8076ducc/robocup-2024/open/mechanical design/camera/raspi spacer.stl

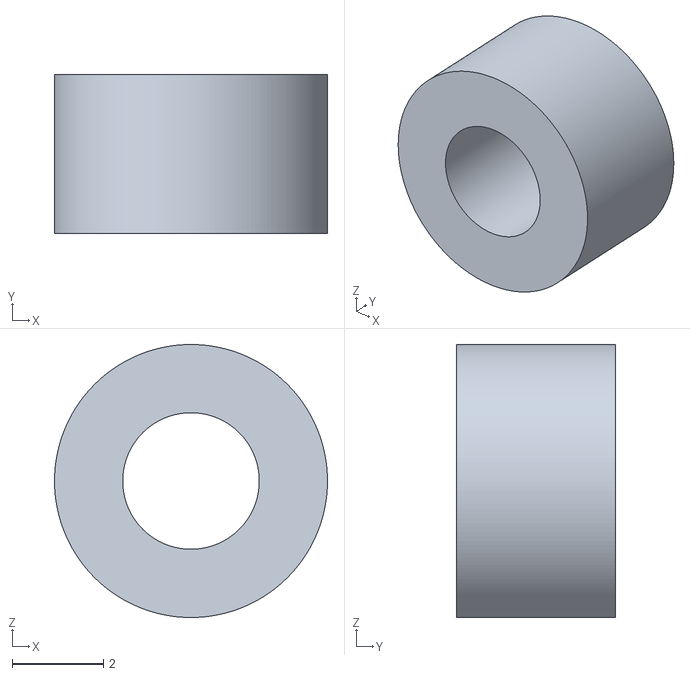
[picture p16: CAD file, 2024-03-23]
open/mechanical design/camera/raspi spacer.stl
6.00 x 3.50 x 6.00
