8076ducc/robocup-2024/open/mechanical design/cycloidal drive/gearbox cover.stl

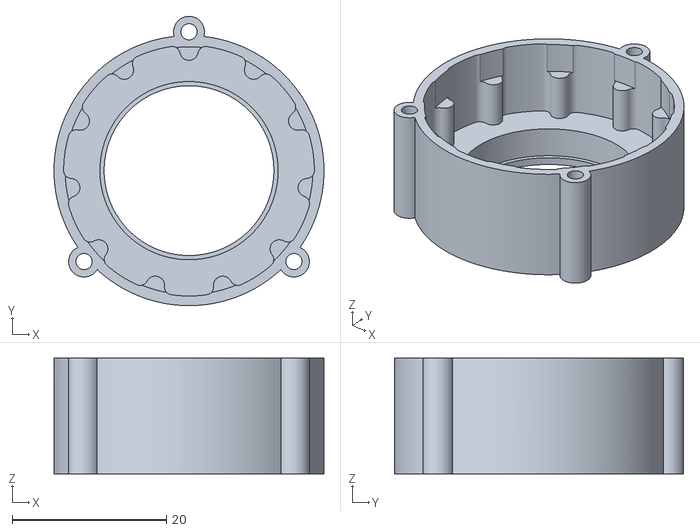
[picture p17: CAD file, 2023-11-01]
open/mechanical design/cycloidal drive/gearbox cover.stl
35.0 x 37.5 x 15.0
