8076ducc/robocup-2024/open/mechanical design/dribbler/dribbler mount.stl

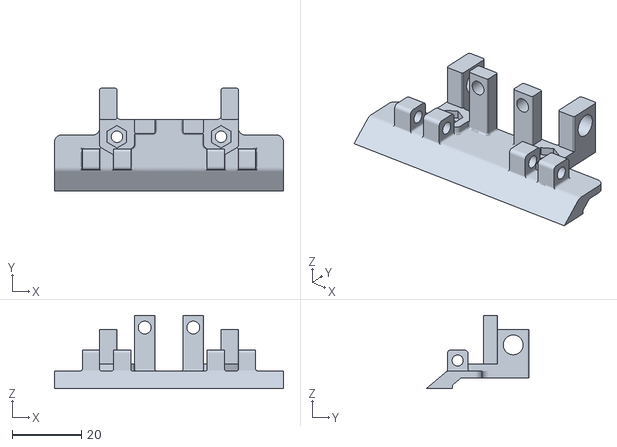
[picture p18: CAD file, 2024-04-01]
open/mechanical design/dribbler/dribbler mount.stl
66.0 x 29.6 x 21.1
