8076ducc/robocup-2024/open/mechanical design/dribbler/mould/big mould.stl

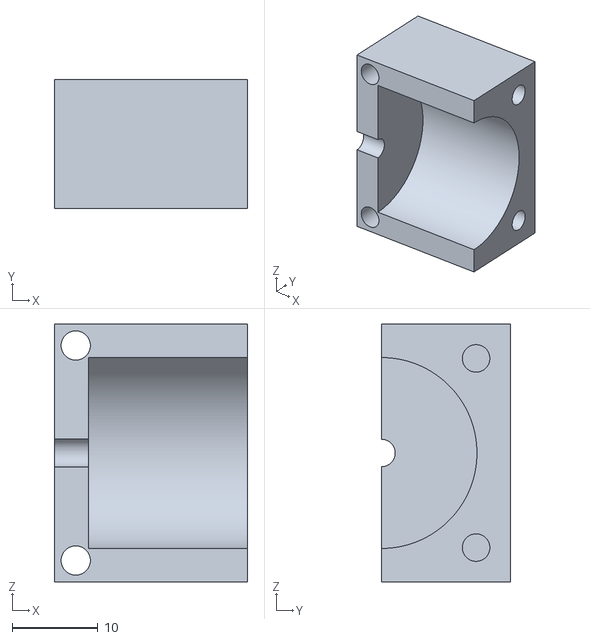
[picture p19: CAD file, 2024-04-05]
open/mechanical design/dribbler/mould/big mould.stl
22.5 x 15.0 x 30.0
