8076ducc/robocup-2024/open/mechanical design/dribbler/test/bearing hole test 6.2.stl

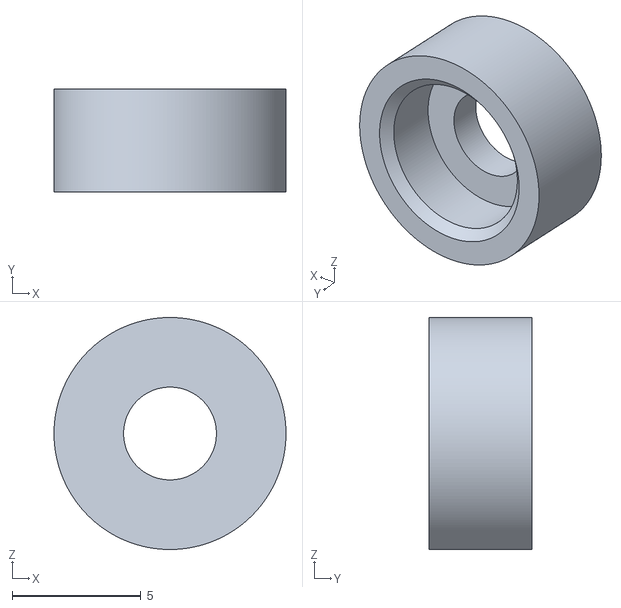
[picture p20: CAD file, 2024-04-04]
open/mechanical design/dribbler/test/bearing hole test 6.2.stl
9.00 x 4.00 x 9.00
