8076ducc/robocup-2024/open/mechanical design/dribbler/v2/gear shield.stl

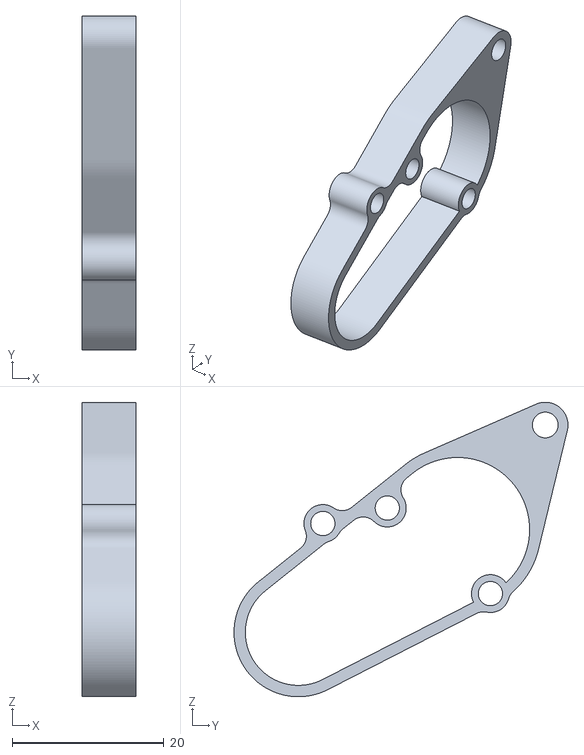
[picture p21: CAD file, 2024-05-06]
open/mechanical design/dribbler/v2/gear shield.stl
7.10 x 44.1 x 38.9
