8076ducc/robocup-2024/open/mechanical design/misc/camera aligner.stl

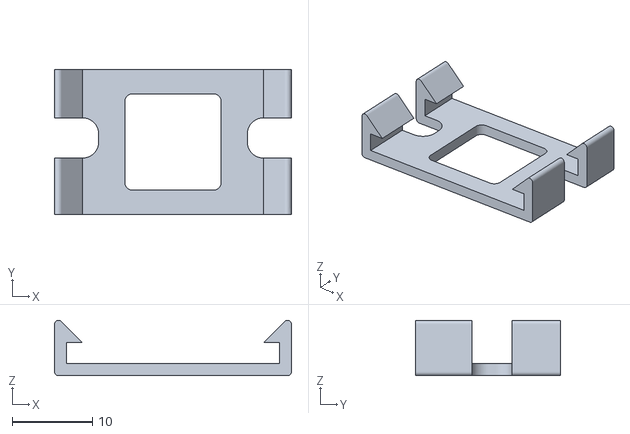
[picture p22: CAD file, 2024-04-01]
open/mechanical design/misc/camera aligner.stl
29.5 x 18.0 x 6.89
