8076ducc/robocup-2024/open/mechanical design/omniwheel/motor spacer.stl

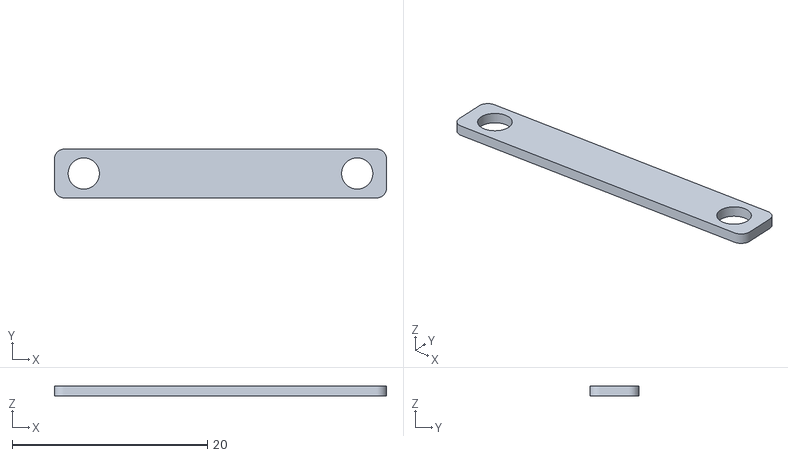
[picture p23: CAD file, 2024-04-01]
open/mechanical design/omniwheel/motor spacer.stl
34.0 x 5.00 x 1.00
