8076ducc/robocup-2024/open/mechanical design/plates/driver/fabrication drawing.dxf

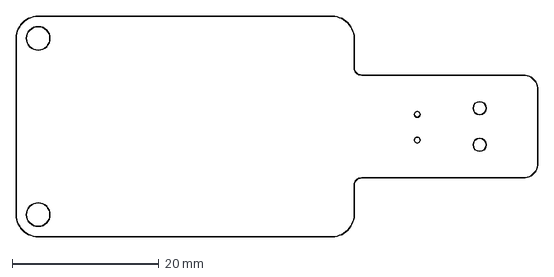
[picture p24: CAD file, 2023-12-15]
open/mechanical design/plates/driver/fabrication drawing.dxf
71.0 x 30.0 mm
