8076ducc/robocup-2024/open/mechanical design/plates/layer 2/fabrication drawing.dxf

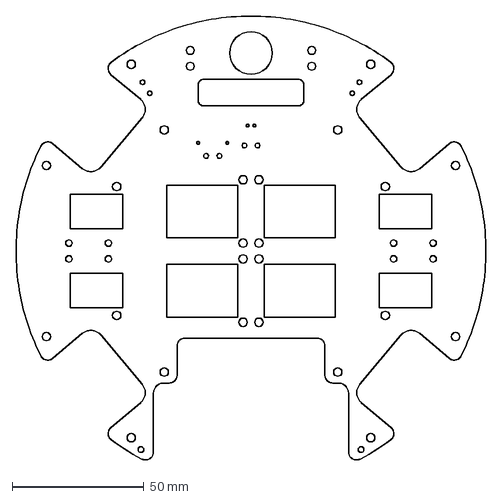
[picture p25: CAD file, 2023-12-15]
open/mechanical design/plates/layer 2/fabrication drawing.dxf
178.0 x 168.1 mm
