8076ducc/robocup-2024/open/mechanical design/plates/layer 3/outline.dxf

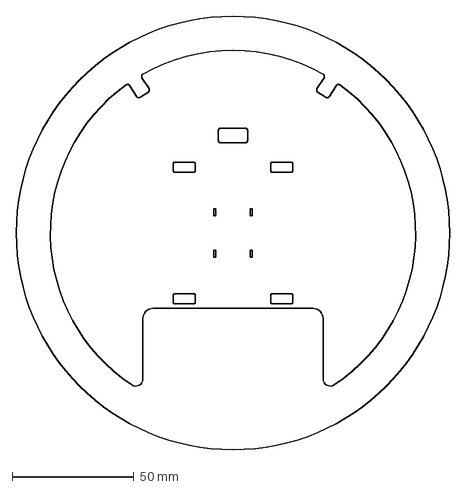
[picture p26: CAD file, 2023-12-17]
open/mechanical design/plates/layer 3/outline.dxf
178.0 x 178.0 mm
