8076ducc/robocup-2024/open/mechanical design/plates/layer 4/layer 4.dxf

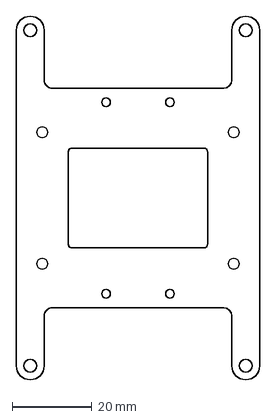
[picture p27: CAD file, 2024-03-23]
open/mechanical design/plates/layer 4/layer 4.dxf
61.0 x 91.2 mm
