8076ducc/robocup-2024/open/mechanical design/plates/Seeed XIAO/drawing.dxf

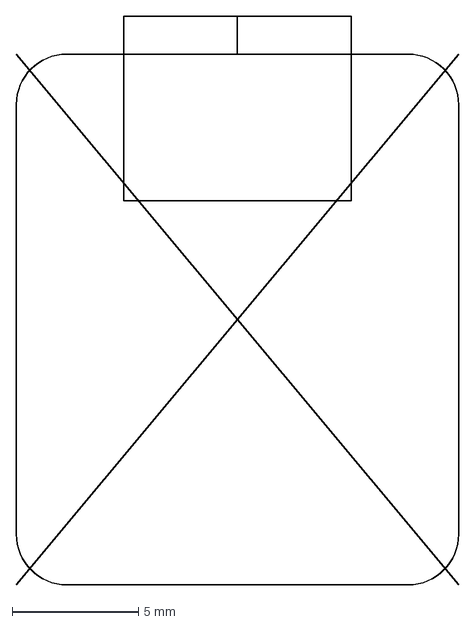
[picture p28: CAD file, 2023-11-23]
open/mechanical design/plates/Seeed XIAO/drawing.dxf
17.5 x 22.5 mm
