8076ducc/robocup-2024/open/mechanical design/shrouds/layer 2 shroud.stl

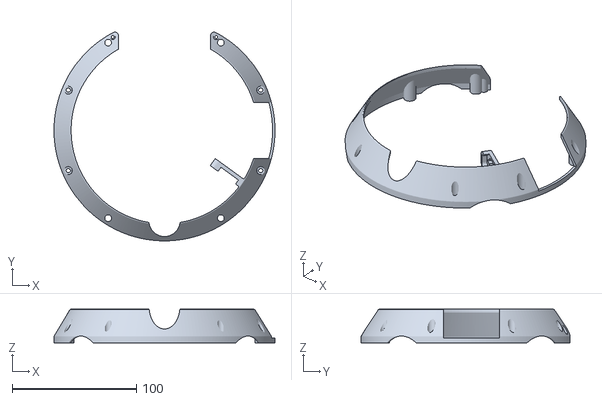
[picture p29: CAD file, 2024-08-02]
open/mechanical design/shrouds/layer 2 shroud.stl
178.0 x 168.1 x 27.0
