8076ducc/robocup-2024/mechanical design/dribbler/dribbler mount v29.stl

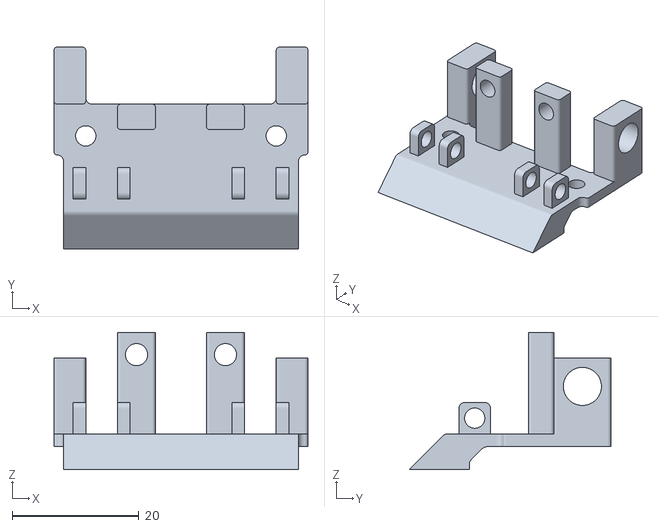
[picture p30: CAD file, 2024-01-17]
mechanical design/dribbler/dribbler mount v29.stl
40.0 x 31.8 x 21.6
