8076ducc/robocup-2024/open/mechanical design/ball puncher/puncher ramp.stl

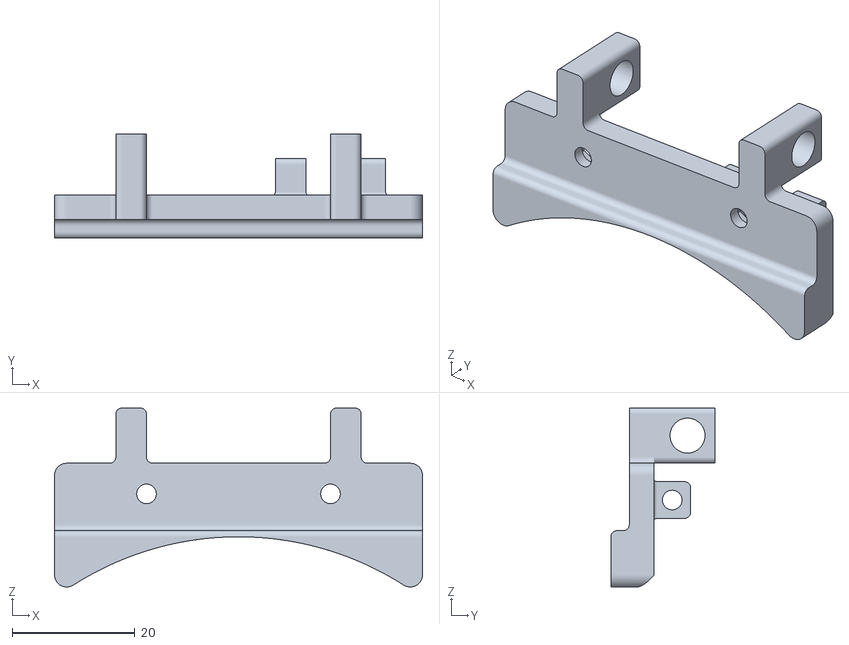
[picture p31: CAD file, 2024-05-06]
open/mechanical design/ball puncher/puncher ramp.stl
60.0 x 17.0 x 29.2
