8076ducc/robocup-2024/open/mechanical design/cycloidal drive/gearbox mount.stl

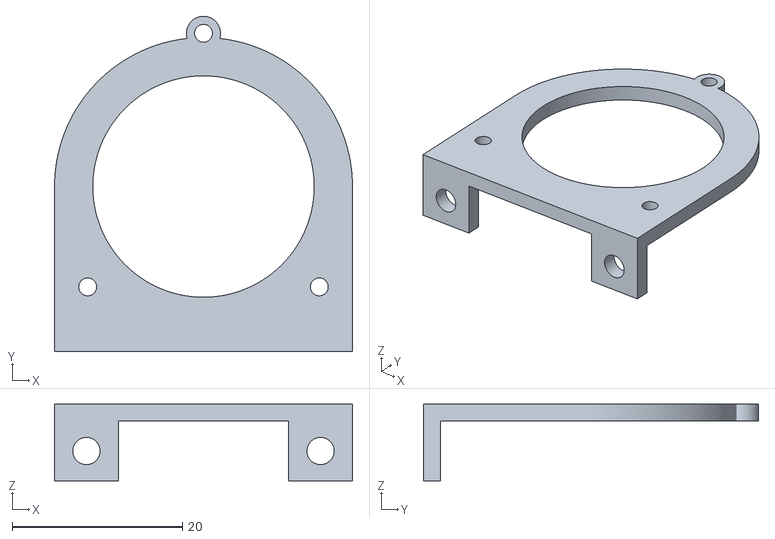
[picture p32: CAD file, 2023-11-01]
open/mechanical design/cycloidal drive/gearbox mount.stl
35.0 x 39.4 x 9.00
