8076ducc/robocup-2024/open/mechanical design/dribbler/gear shield.stl

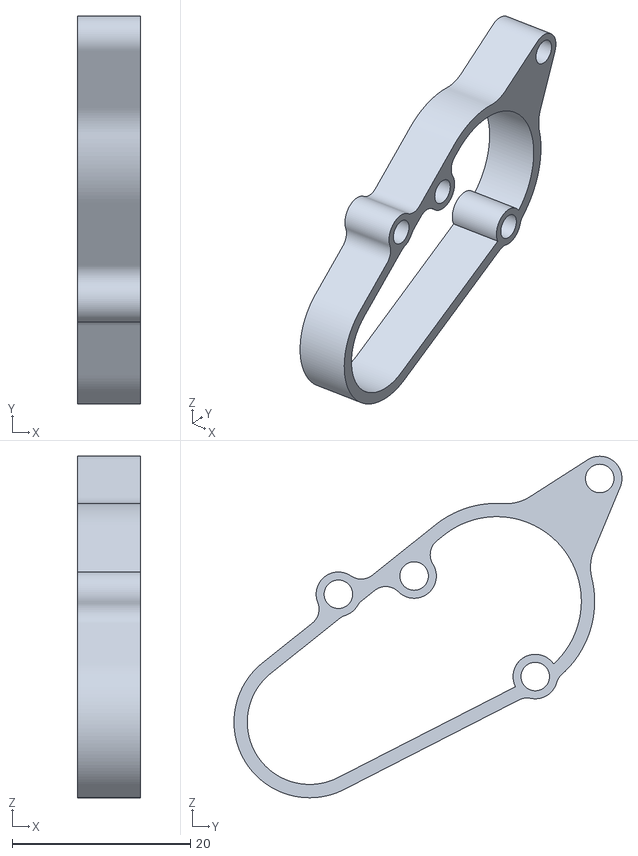
[picture p33: CAD file, 2024-04-01]
open/mechanical design/dribbler/gear shield.stl
7.10 x 43.6 x 38.4
