8076ducc/robocup-2024/open/mechanical design/dribbler/mould/small mould.stl

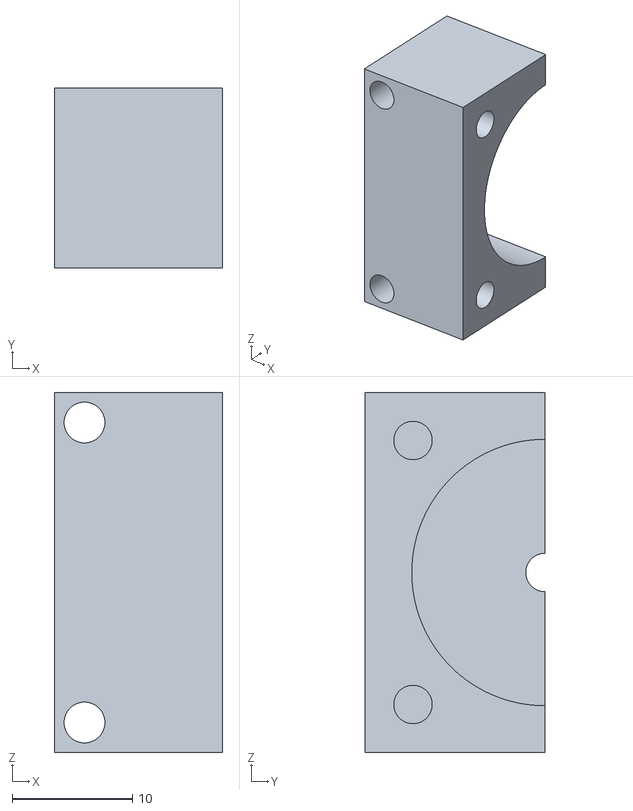
[picture p34: CAD file, 2024-02-21]
open/mechanical design/dribbler/mould/small mould.stl
14.0 x 15.0 x 30.0
