8076ducc/robocup-2024/open/mechanical design/dribbler/v2/plate (right).stl

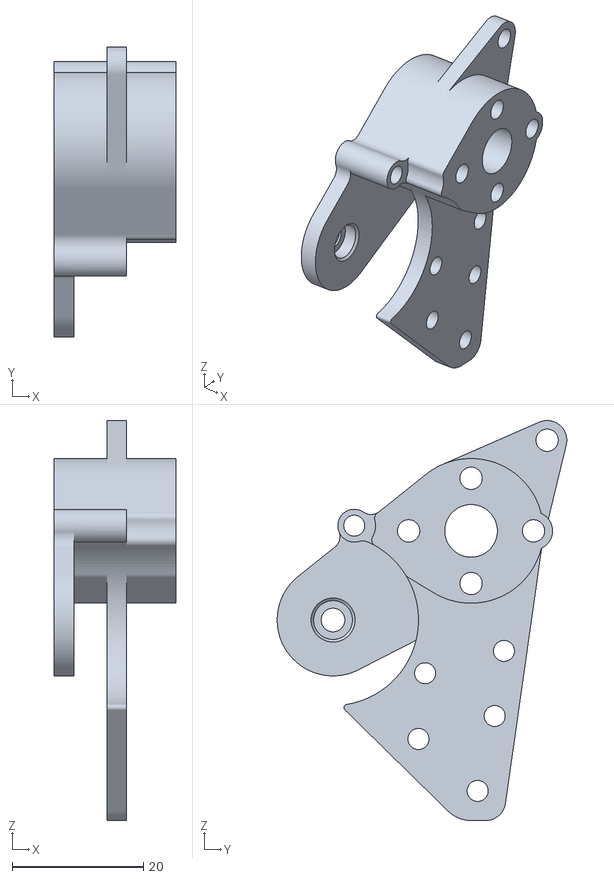
[picture p35: CAD file, 2024-04-05]
open/mechanical design/dribbler/v2/plate (right).stl
18.5 x 44.1 x 60.8
