8076ducc/robocup-2024/open/mechanical design/misc/wire clip.stl

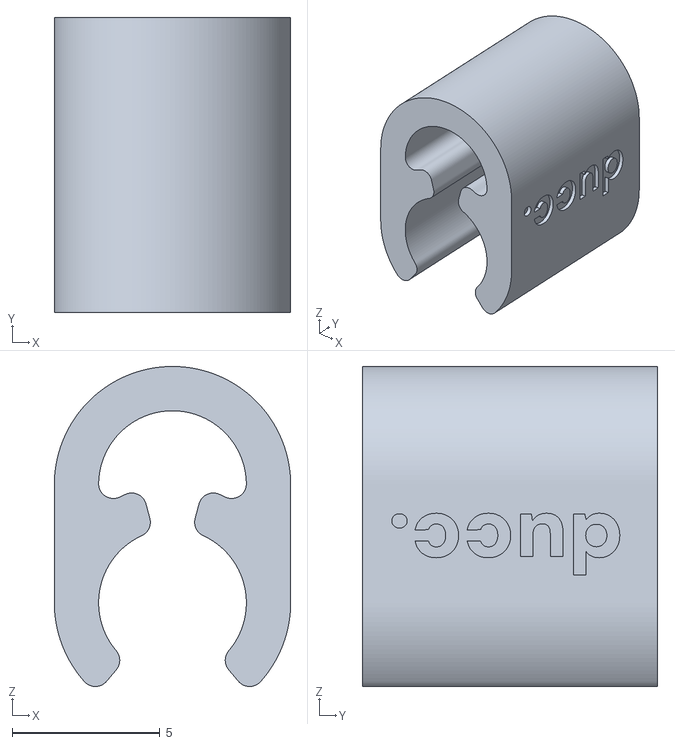
[picture p36: CAD file, 2024-03-23]
open/mechanical design/misc/wire clip.stl
8.00 x 10.0 x 10.8
