8076ducc/robocup-2024/open/mechanical design/omniwheel/roller.stl

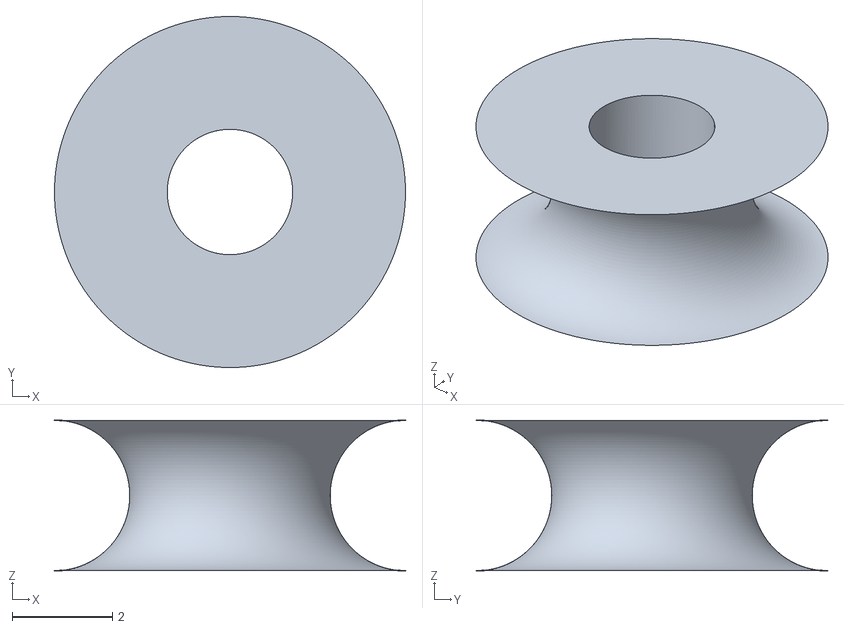
[picture p37: CAD file, 2024-04-01]
open/mechanical design/omniwheel/roller.stl
7.00 x 7.00 x 3.00
