8076ducc/robocup-2024/open/mechanical design/plates/layer 3/fabrication drawing.dxf

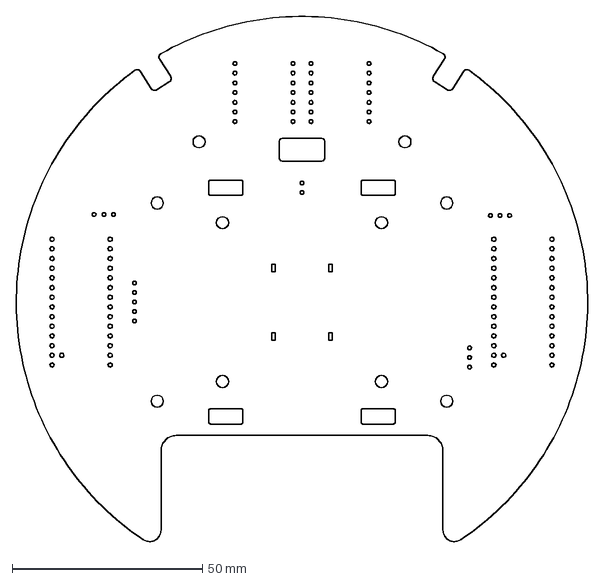
[picture p39: CAD file, 2023-12-15]
open/mechanical design/plates/layer 3/fabrication drawing.dxf
150.0 x 137.9 mm
