8076ducc/robocup-2024/open/mechanical design/plates/layer 4/layer 4.5.dxf

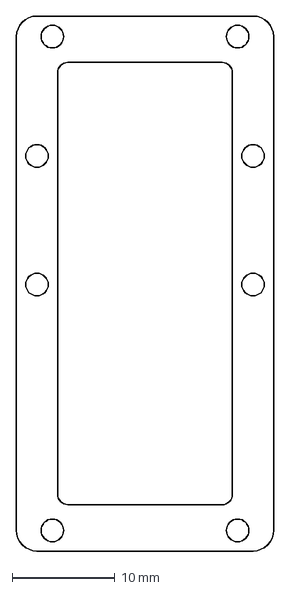
[picture p40: CAD file, 2024-03-23]
open/mechanical design/plates/layer 4/layer 4.5.dxf
25.0 x 52.0 mm
