8076ducc/robocup-2024/open/mechanical design/shrouds/layer 1 short cover.stl

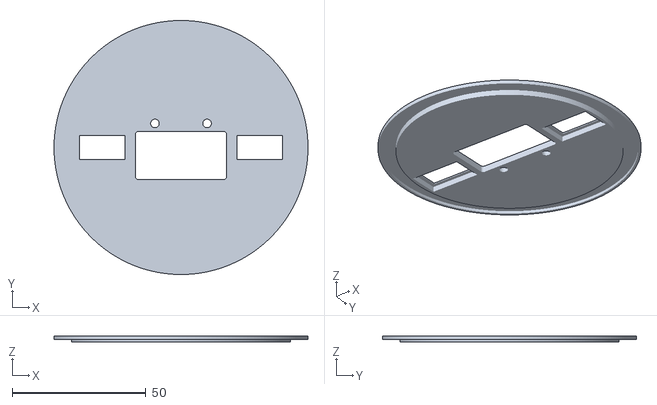
[picture p41: CAD file, 2024-08-02]
open/mechanical design/shrouds/layer 1 short cover.stl
95.0 x 95.0 x 2.40
