8076ducc/robocup-2024/mechanical design/dribbler/spacer.stl

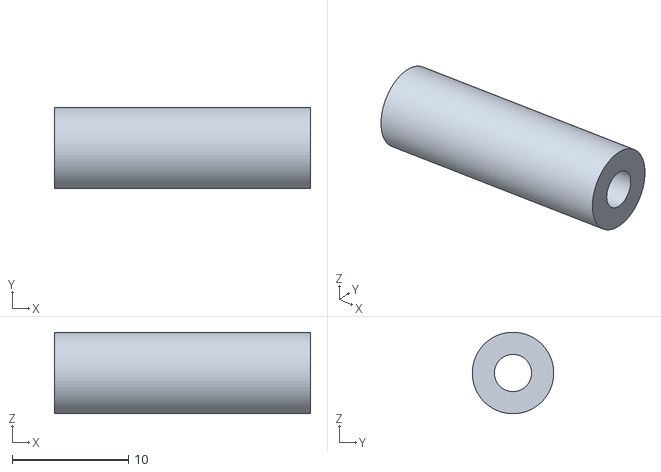
[picture p42: CAD file, 2024-01-17]
mechanical design/dribbler/spacer.stl
22.0 x 7.00 x 7.00
