8076ducc/robocup-2024/open/mechanical design/ball puncher/plate (right).stl

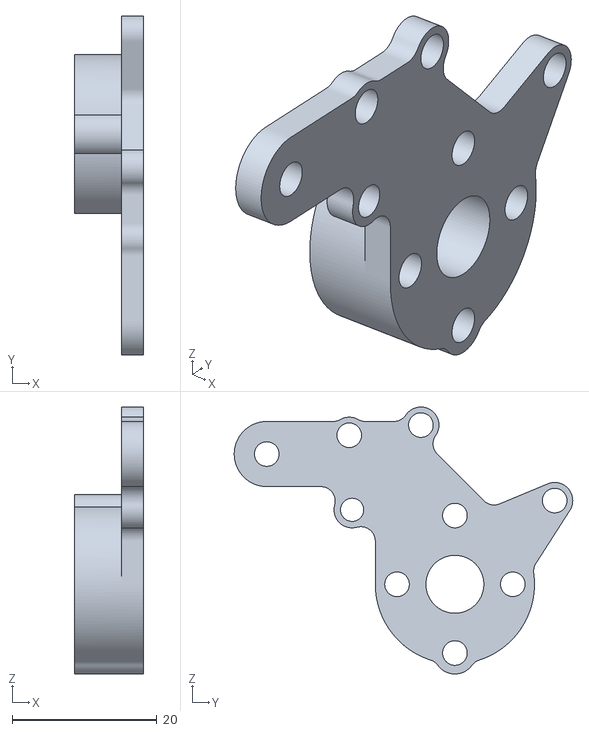
[picture p43: CAD file, 2024-05-06]
open/mechanical design/ball puncher/plate (right).stl
9.50 x 46.8 x 36.9
