8076ducc/robocup-2024/open/mechanical design/cycloidal drive/motor mount.stl

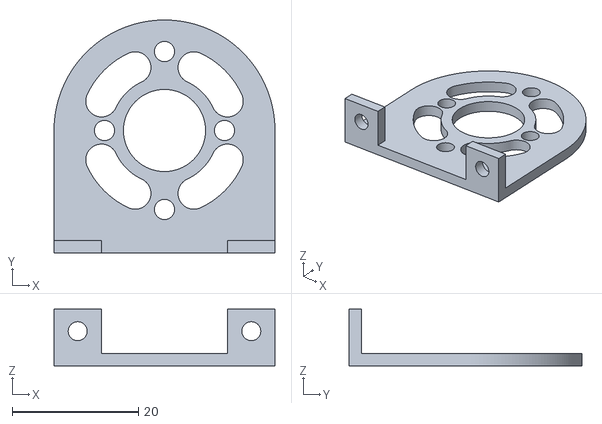
[picture p44: CAD file, 2023-11-01]
open/mechanical design/cycloidal drive/motor mount.stl
35.0 x 36.9 x 9.00
