8076ducc/robocup-2024/open/mechanical design/dribbler/emax spacer.stl

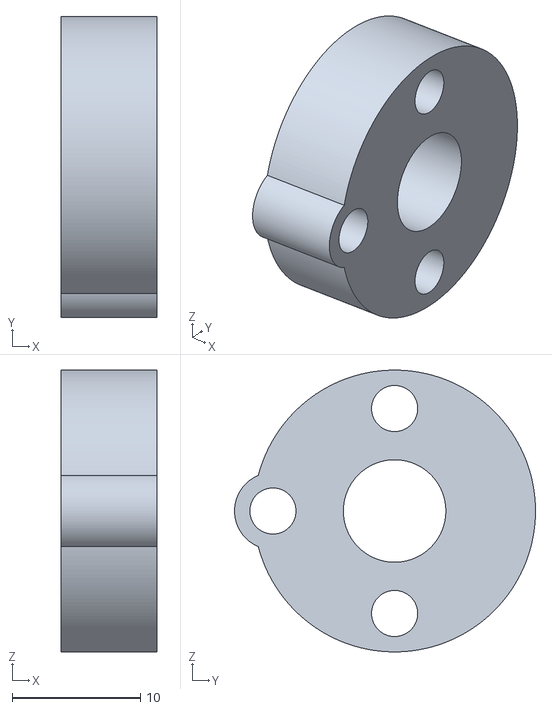
[picture p45: CAD file, 2024-04-01]
open/mechanical design/dribbler/emax spacer.stl
7.50 x 23.5 x 22.0
