8076ducc/robocup-2024/open/mechanical design/dribbler/mould/big roller.stl

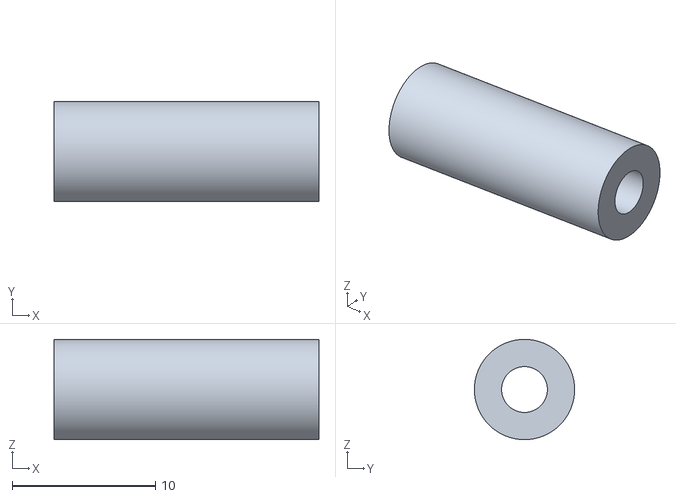
[picture p46: CAD file, 2024-02-21]
open/mechanical design/dribbler/mould/big roller.stl
18.5 x 7.00 x 7.00
