8076ducc/robocup-2024/open/mechanical design/dribbler/v2/clasp.stl

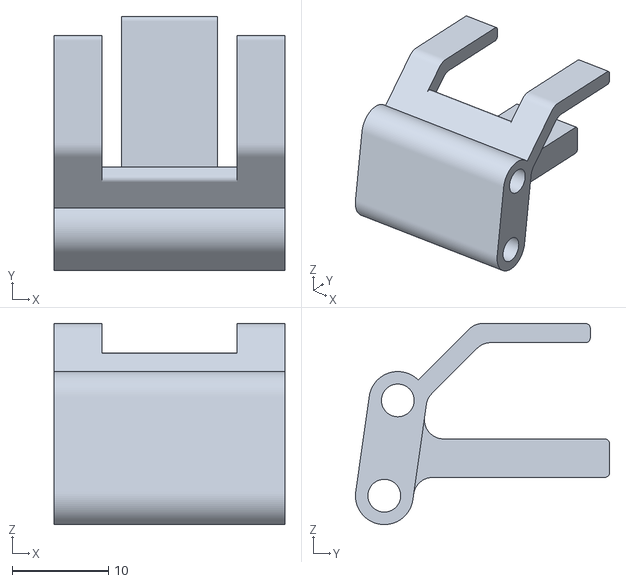
[picture p47: CAD file, 2024-04-05]
open/mechanical design/dribbler/v2/clasp.stl
24.0 x 26.4 x 20.9
