8076ducc/robocup-2024/open/mechanical design/misc/tensegrity.stl

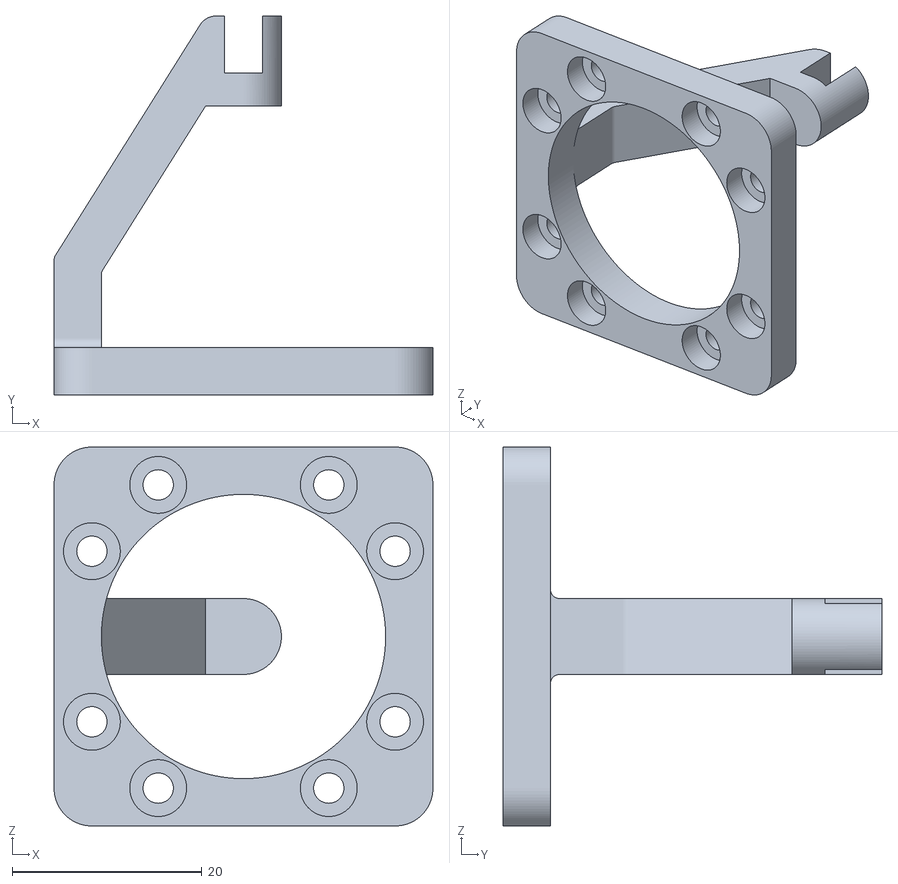
[picture p48: CAD file, 2024-02-19]
open/mechanical design/misc/tensegrity.stl
40.0 x 40.0 x 40.0
