8076ducc/robocup-2024/open/mechanical design/omniwheel/omniwheel housing.stl

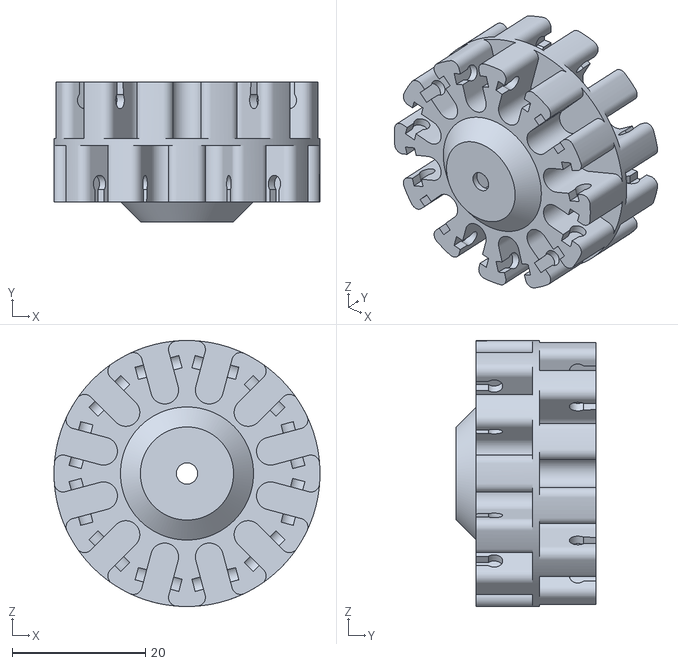
[picture p49: CAD file, 2024-04-01]
open/mechanical design/omniwheel/omniwheel housing.stl
40.0 x 21.0 x 40.0
