8076ducc/robocup-2024/open/mechanical design/plates/layer 1/outline.dxf

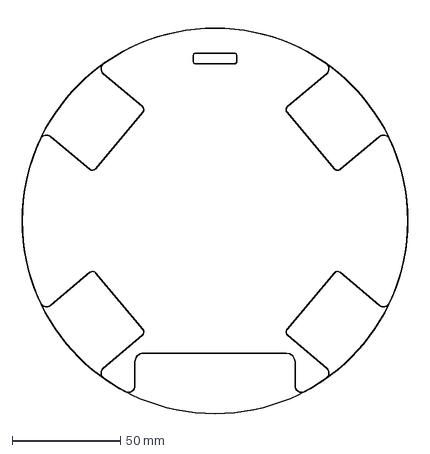
[picture p50: CAD file, 2023-11-23]
open/mechanical design/plates/layer 1/outline.dxf
183.7 x 183.4 mm
