8076ducc/robocup-2024/open/mechanical design/plates/layer 2/outline.dxf

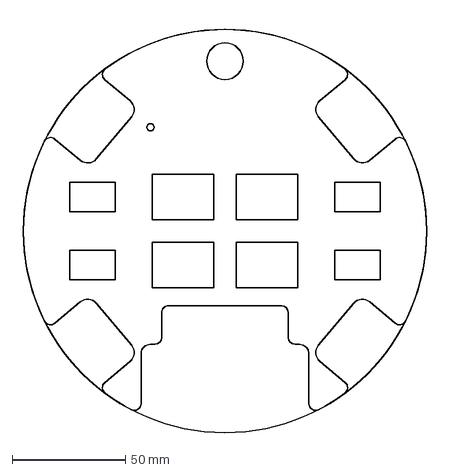
[picture p51: CAD file, 2023-11-23]
open/mechanical design/plates/layer 2/outline.dxf
184.2 x 183.8 mm
