8076ducc/robocup-2024/open/mechanical design/plates/layer 4/layer 5.dxf

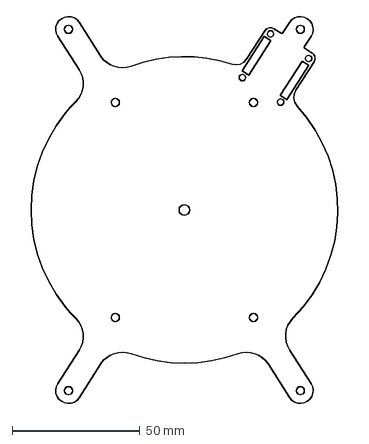
[picture p52: CAD file, 2024-03-23]
open/mechanical design/plates/layer 4/layer 5.dxf
131.8 x 151.5 mm
