8076ducc/robocup-2024/open/mechanical design/shrouds/layer 1 (back).stl

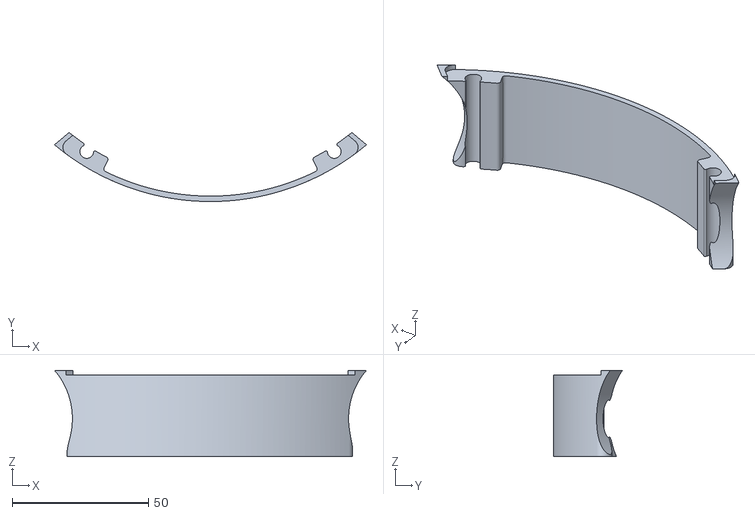
[picture p53: CAD file, 2024-04-01]
open/mechanical design/shrouds/layer 1 (back).stl
114.4 x 25.3 x 31.6
