8076ducc/robocup-2024/mechanical design/dribbler/roller cover.stl

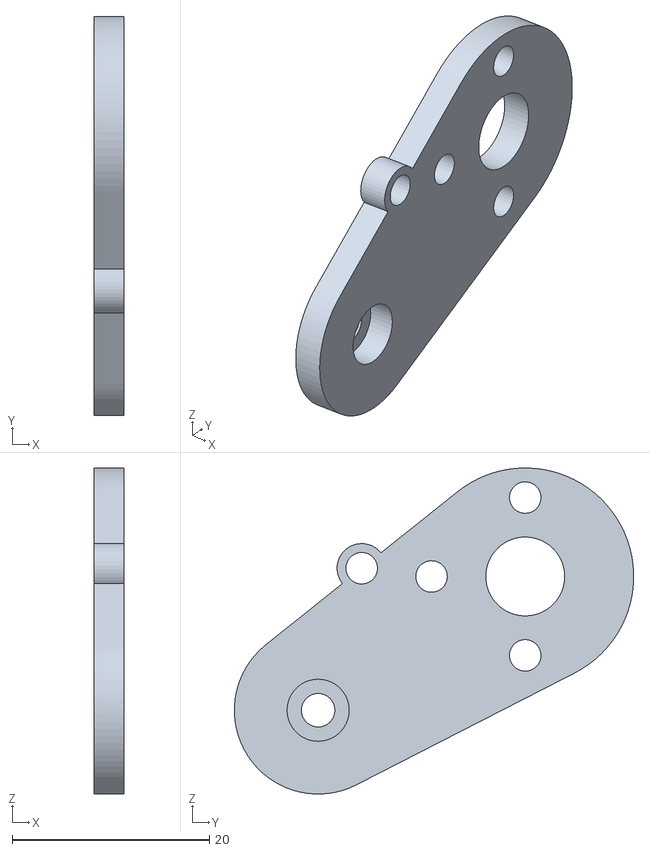
[picture p54: CAD file, 2024-01-17]
mechanical design/dribbler/roller cover.stl
3.00 x 40.5 x 33.1
