8076ducc/robocup-2024/open/mechanical design/dribbler/mould/small roller.stl

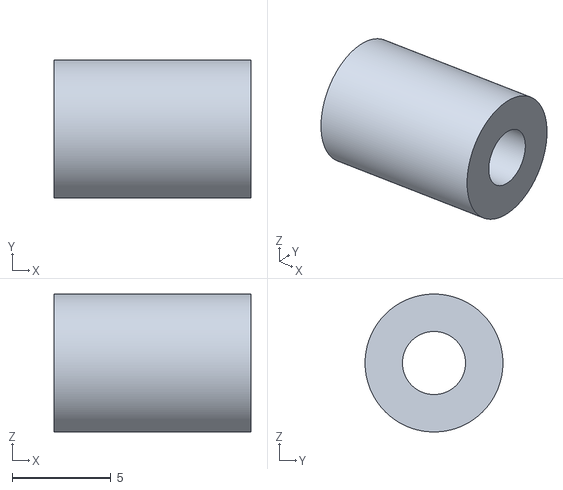
[picture p55: CAD file, 2024-02-21]
open/mechanical design/dribbler/mould/small roller.stl
10.0 x 7.00 x 7.00
