8076ducc/robocup-2024/open/mechanical design/dribbler/plate (left).stl

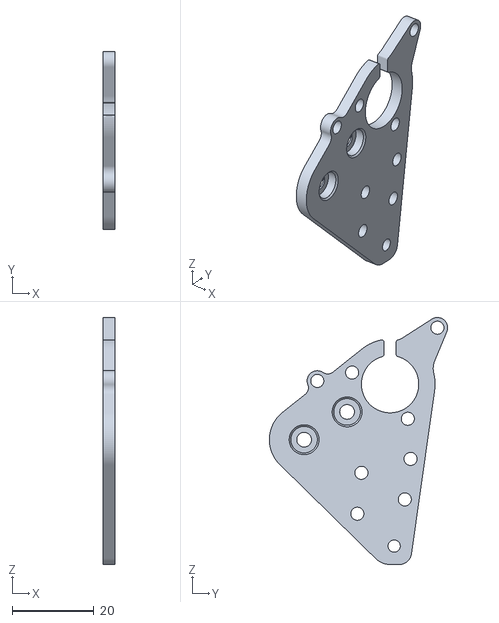
[picture p56: CAD file, 2024-04-01]
open/mechanical design/dribbler/plate (left).stl
3.00 x 43.6 x 60.3
