8076ducc/robocup-2024/open/mechanical design/dribbler/v2/plate (left).stl

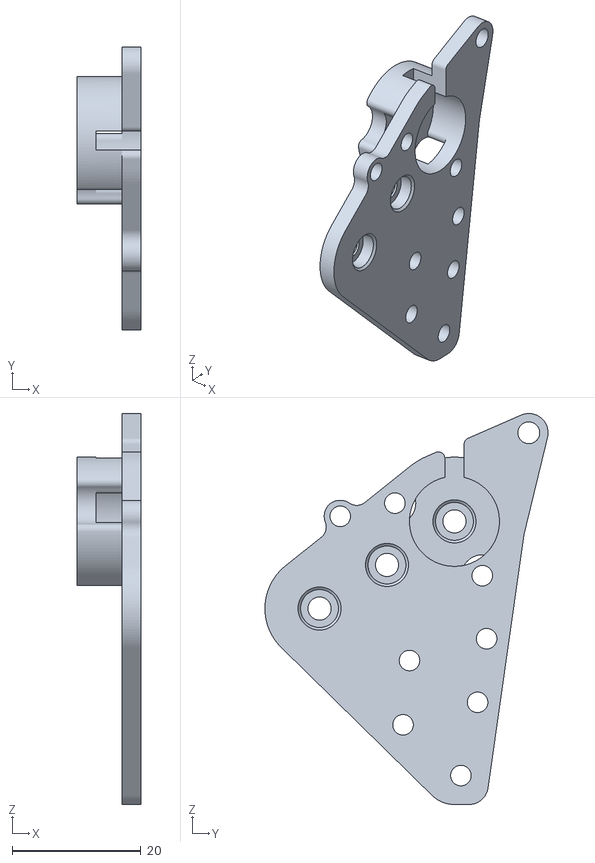
[picture p57: CAD file, 2024-04-04]
open/mechanical design/dribbler/v2/plate (left).stl
10.0 x 44.1 x 60.8
