8076ducc/robocup-2024/open/mechanical design/misc/band holder.stl

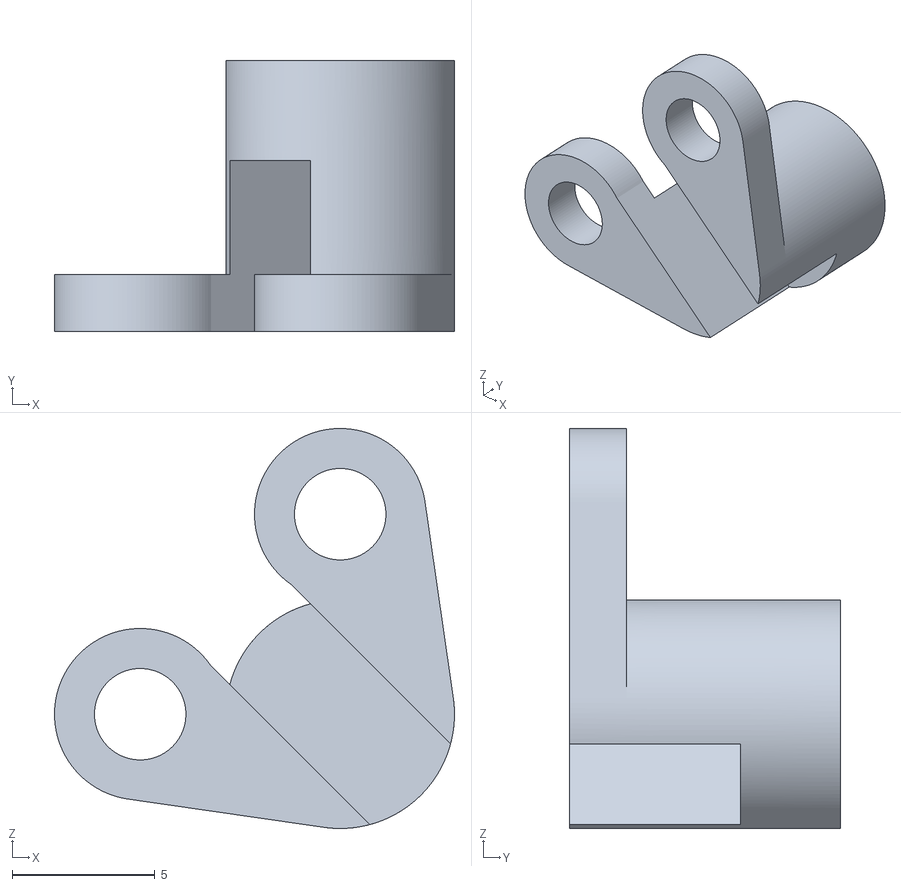
[picture p58: CAD file, 2024-02-19]
open/mechanical design/misc/band holder.stl
14.0 x 9.50 x 14.0
