8076ducc/robocup-2024/mechanical design/dribbler/roller (left).stl

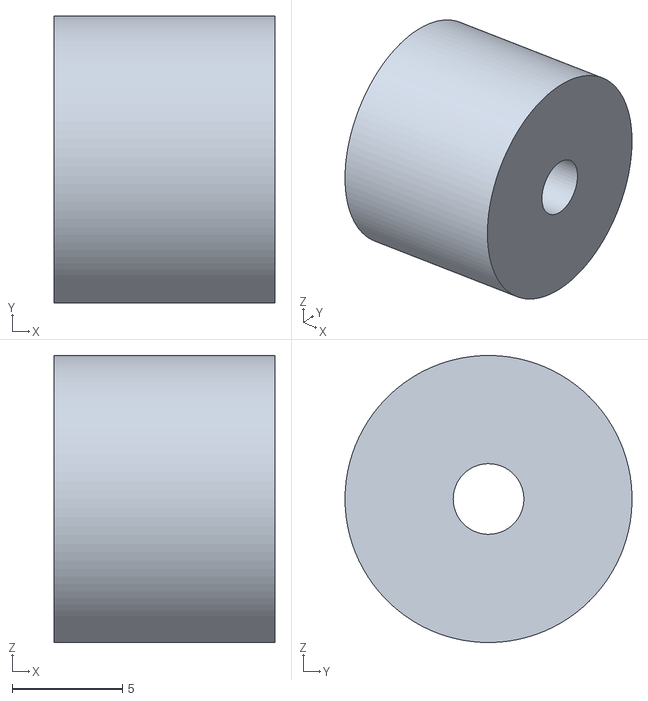
[picture p60: CAD file, 2024-01-17]
mechanical design/dribbler/roller (left).stl
10.0 x 13.0 x 13.0
