8076ducc/robocup-2024/open/mechanical design/dribbler/gear cover.stl

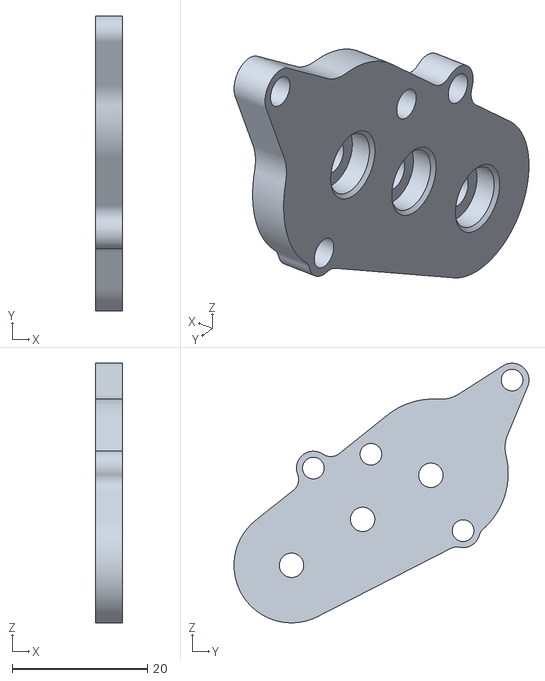
[picture p61: CAD file, 2024-04-01]
open/mechanical design/dribbler/gear cover.stl
4.00 x 43.6 x 38.4
