8076ducc/robocup-2024/open/mechanical design/dribbler/mould/mould (top).stl

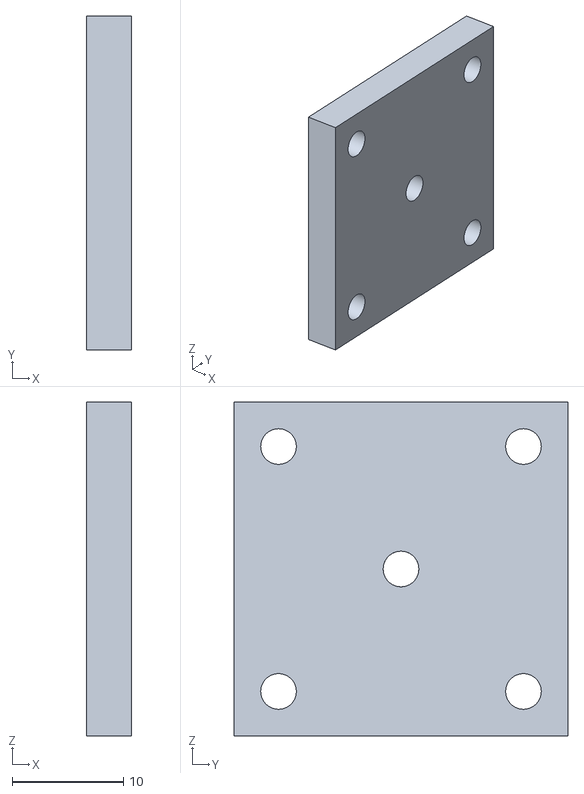
[picture p62: CAD file, 2024-02-21]
open/mechanical design/dribbler/mould/mould (top).stl
4.00 x 30.0 x 30.0
