8076ducc/robocup-2024/open/mechanical design/shrouds/layer 1 (right).stl

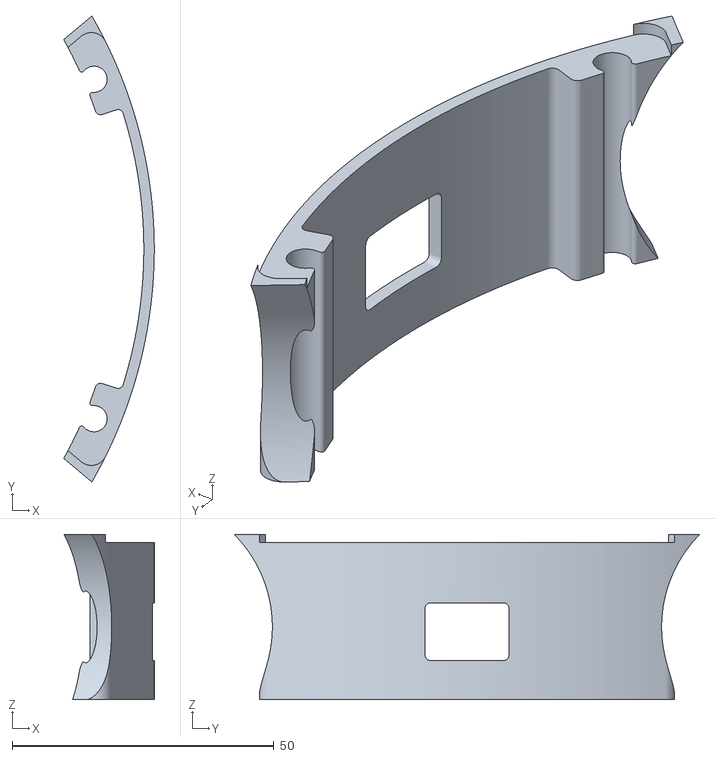
[picture p63: CAD file, 2024-04-01]
open/mechanical design/shrouds/layer 1 (right).stl
17.3 x 89.0 x 31.6
