8076ducc/robocup-2024/mechanical design/dribbler/roller (right).stl

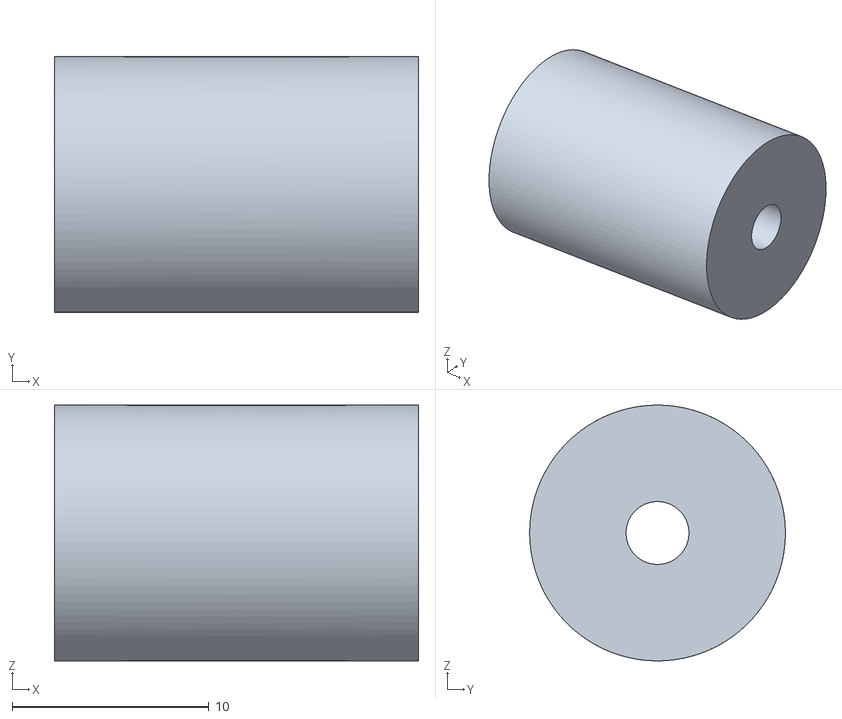
[picture p64: CAD file, 2024-01-17]
mechanical design/dribbler/roller (right).stl
18.5 x 13.0 x 13.0
