8076ducc/robocup-2024/open/mechanical design/dribbler/plate (right).stl

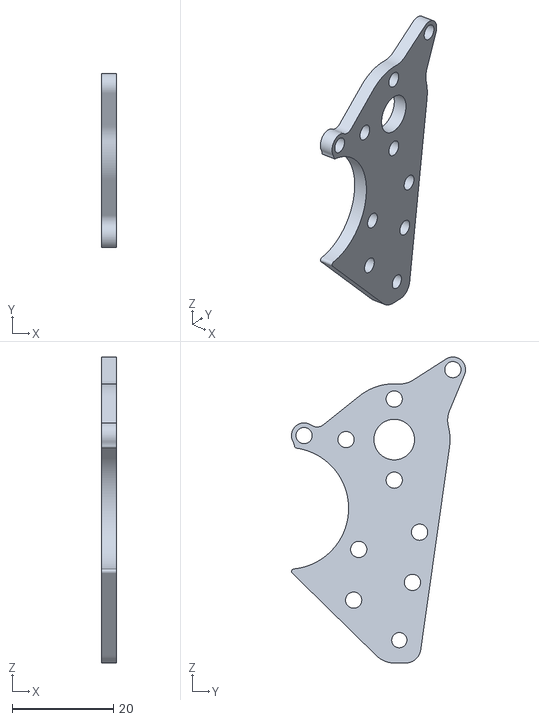
[picture p65: CAD file, 2024-04-01]
open/mechanical design/dribbler/plate (right).stl
3.00 x 34.3 x 60.3
