8076ducc/robocup-2024/open/mechanical design/dribbler/v2/gear cover.stl

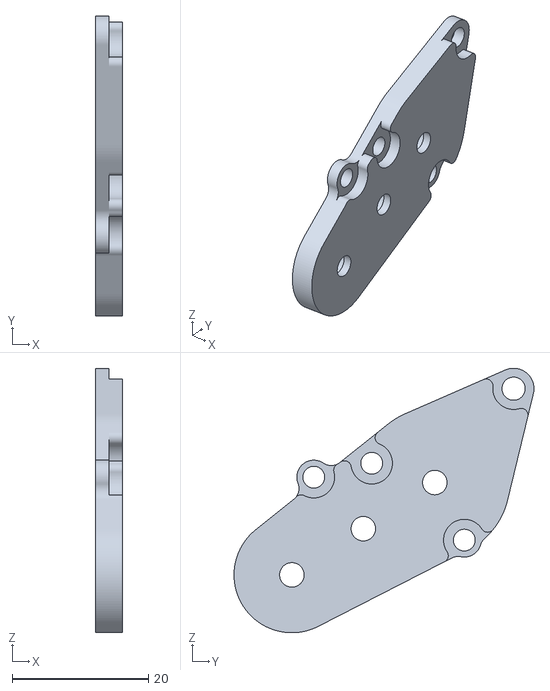
[picture p66: CAD file, 2024-04-04]
open/mechanical design/dribbler/v2/gear cover.stl
4.00 x 44.1 x 38.9
