8076ducc/robocup-2024/open/mechanical design/shrouds/layer 1 (front right).stl

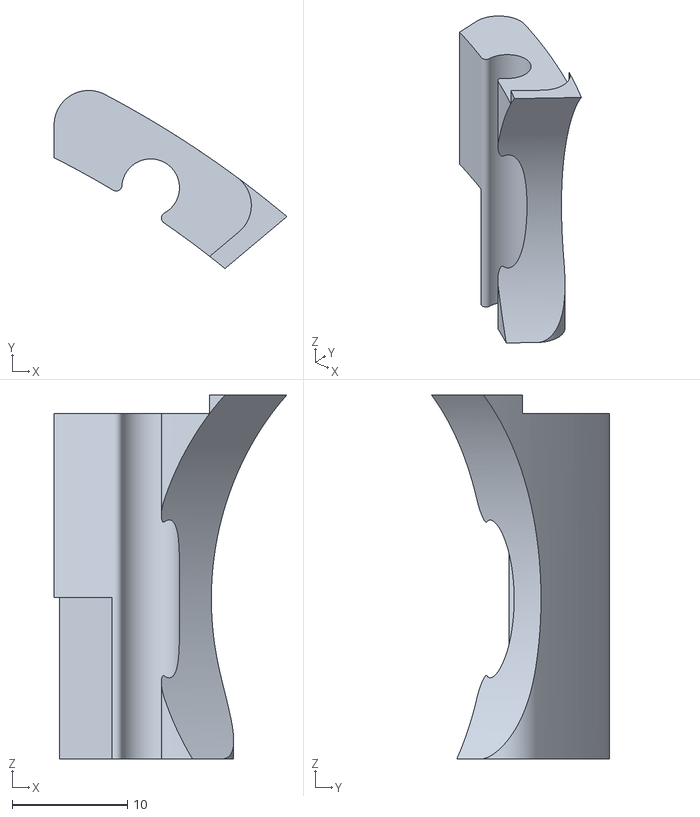
[picture p67: CAD file, 2024-04-01]
open/mechanical design/shrouds/layer 1 (front right).stl
20.2 x 15.5 x 31.6
