8076ducc/robocup-2024/mechanical design/dribbler/gear cover.stl

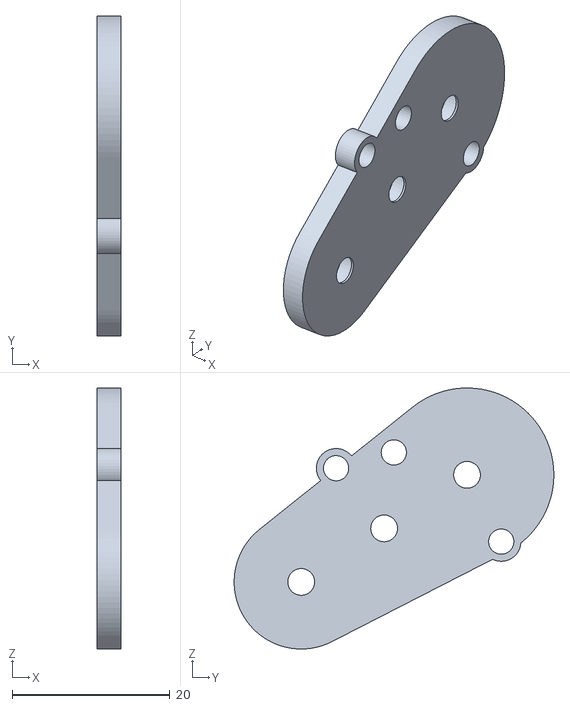
[picture p68: CAD file, 2024-01-17]
mechanical design/dribbler/gear cover.stl
3.00 x 40.5 x 33.1
