8076ducc/robocup-2024/open/mechanical design/dribbler/v2/spacer.stl

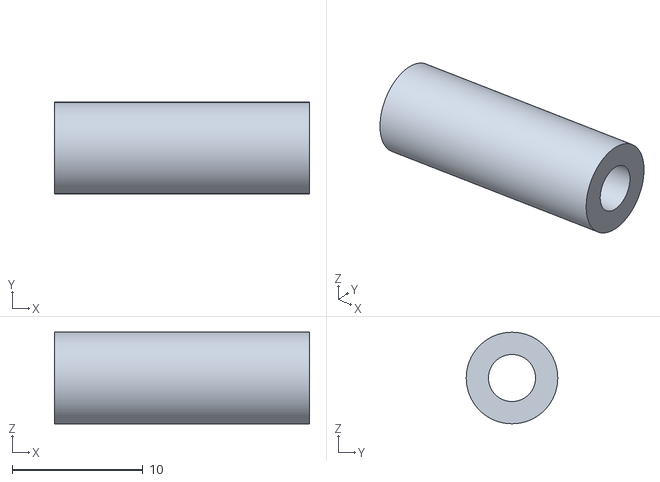
[picture p69: CAD file, 2024-04-01]
open/mechanical design/dribbler/v2/spacer.stl
19.5 x 7.00 x 7.00
