8076ducc/robocup-2024/open/mechanical design/shrouds/layer 1 (left).stl

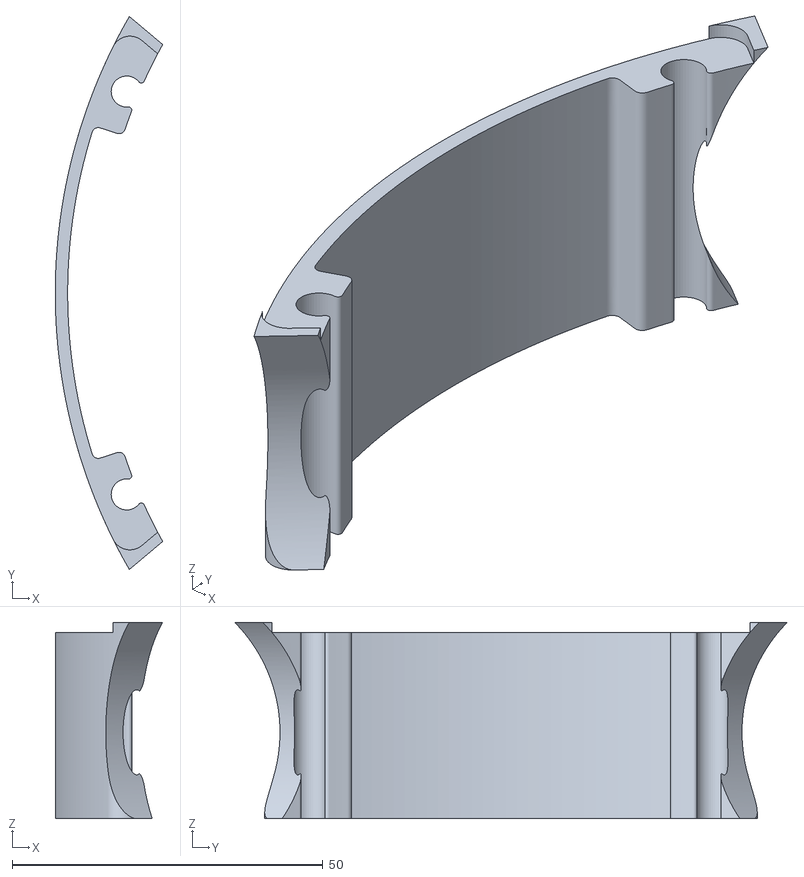
[picture p70: CAD file, 2024-04-01]
open/mechanical design/shrouds/layer 1 (left).stl
17.3 x 89.0 x 31.6
