8076ducc/robocup-2024/mechanical design/dribbler/kicker plate v6.stl

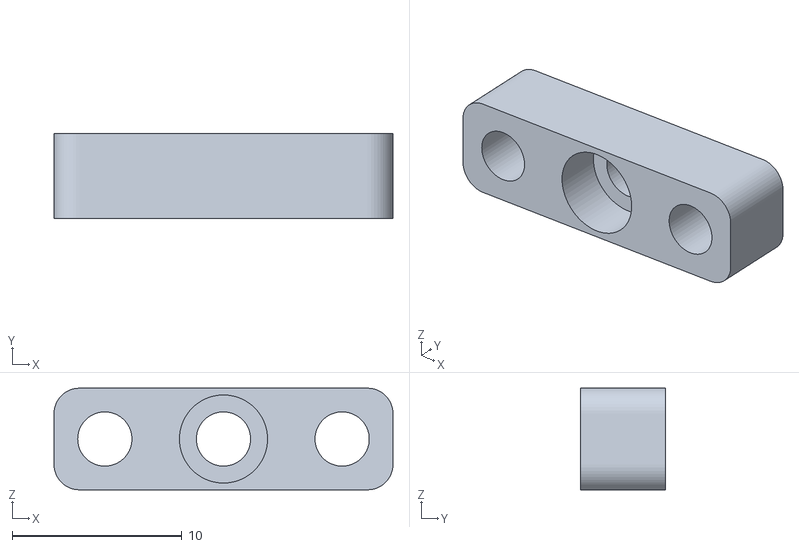
[picture p71: CAD file, 2024-01-17]
mechanical design/dribbler/kicker plate v6.stl
20.0 x 5.00 x 6.00
