8076ducc/robocup-2024/open/mechanical design/dribbler/clasp.stl

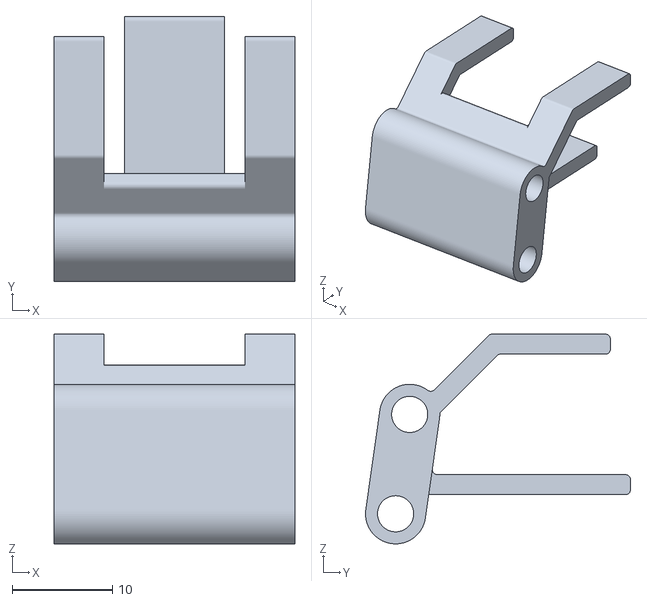
[picture p72: CAD file, 2024-04-01]
open/mechanical design/dribbler/clasp.stl
24.0 x 26.4 x 20.9
