8076ducc/robocup-2024/open/mechanical design/dribbler/v2/roller cover.stl

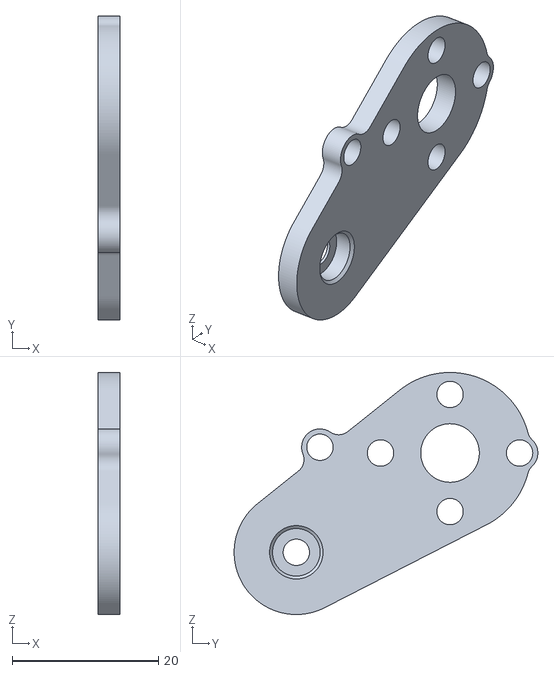
[picture p73: CAD file, 2024-04-01]
open/mechanical design/dribbler/v2/roller cover.stl
3.00 x 41.5 x 33.1
