8076ducc/robocup-2024/mechanical design/dribbler/plate (right).stl

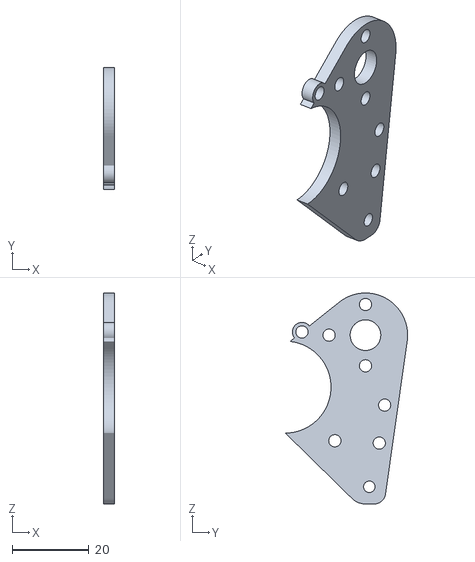
[picture p74: CAD file, 2024-01-01]
mechanical design/dribbler/plate (right).stl
3.00 x 31.9 x 55.1
