8076ducc/robocup-2024/mechanical design/dribbler/ramp.stl

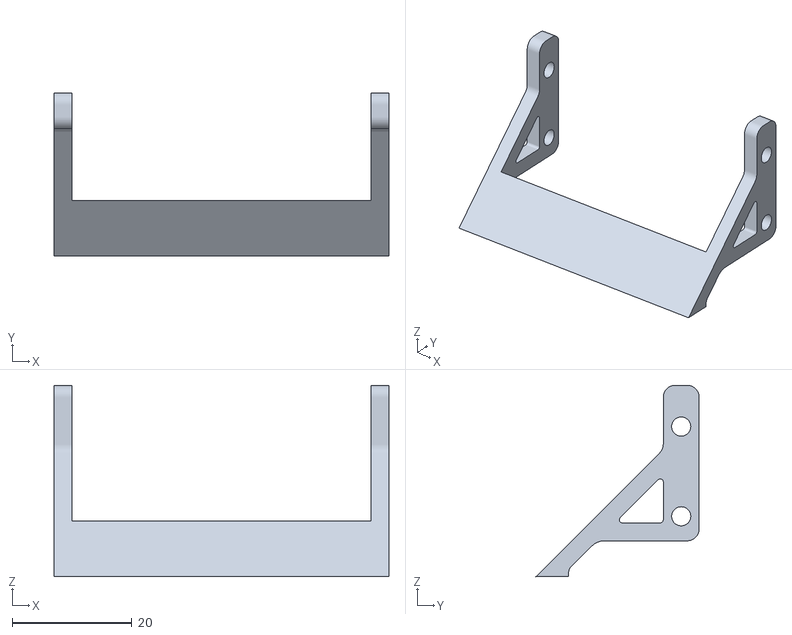
[picture p75: CAD file, 2023-11-01]
mechanical design/dribbler/ramp.stl
56.0 x 27.3 x 32.0
