8076ducc/robocup-2024/mechanical design/dribbler/silicone valley (big).stl

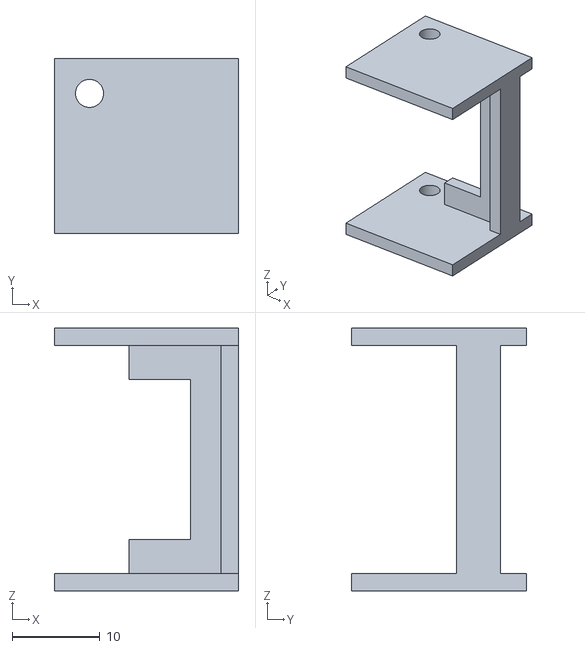
[picture p76: CAD file, 2023-11-01]
mechanical design/dribbler/silicone valley (big).stl
21.0 x 20.0 x 30.0
