8076ducc/robocup-2024/mechanical design/dribbler/gear shield (5mm gear).stl

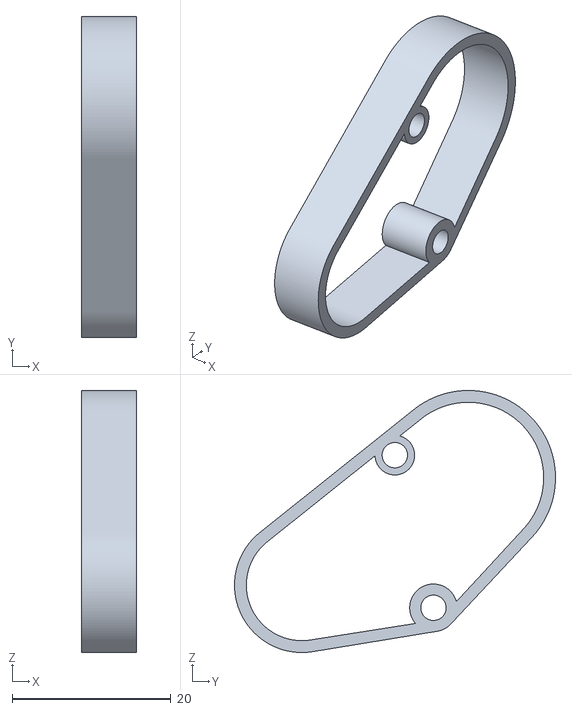
[picture p77: CAD file, 2023-11-01]
mechanical design/dribbler/gear shield (5mm gear).stl
7.00 x 40.5 x 33.1
