8076ducc/robocup-2024/mechanical design/dribbler/gear shield (3mm gear).stl

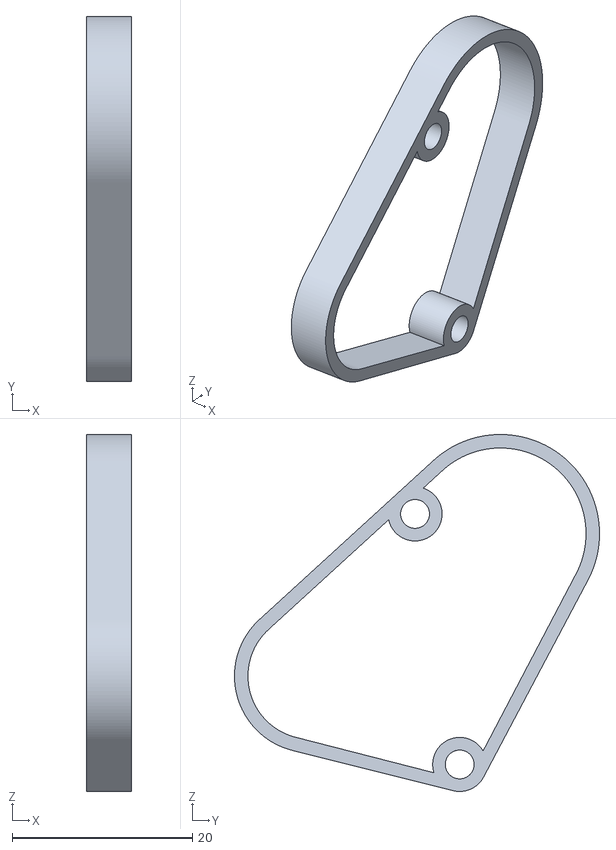
[picture p78: CAD file, 2023-10-21]
mechanical design/dribbler/gear shield (3mm gear).stl
5.00 x 40.5 x 39.6
