8076ducc/robocup-2024/lightweight/layer1/layer1.kicad_sch

## KiCad design lightweight/layer1/layer1.kicad_sch (2024-01-02)

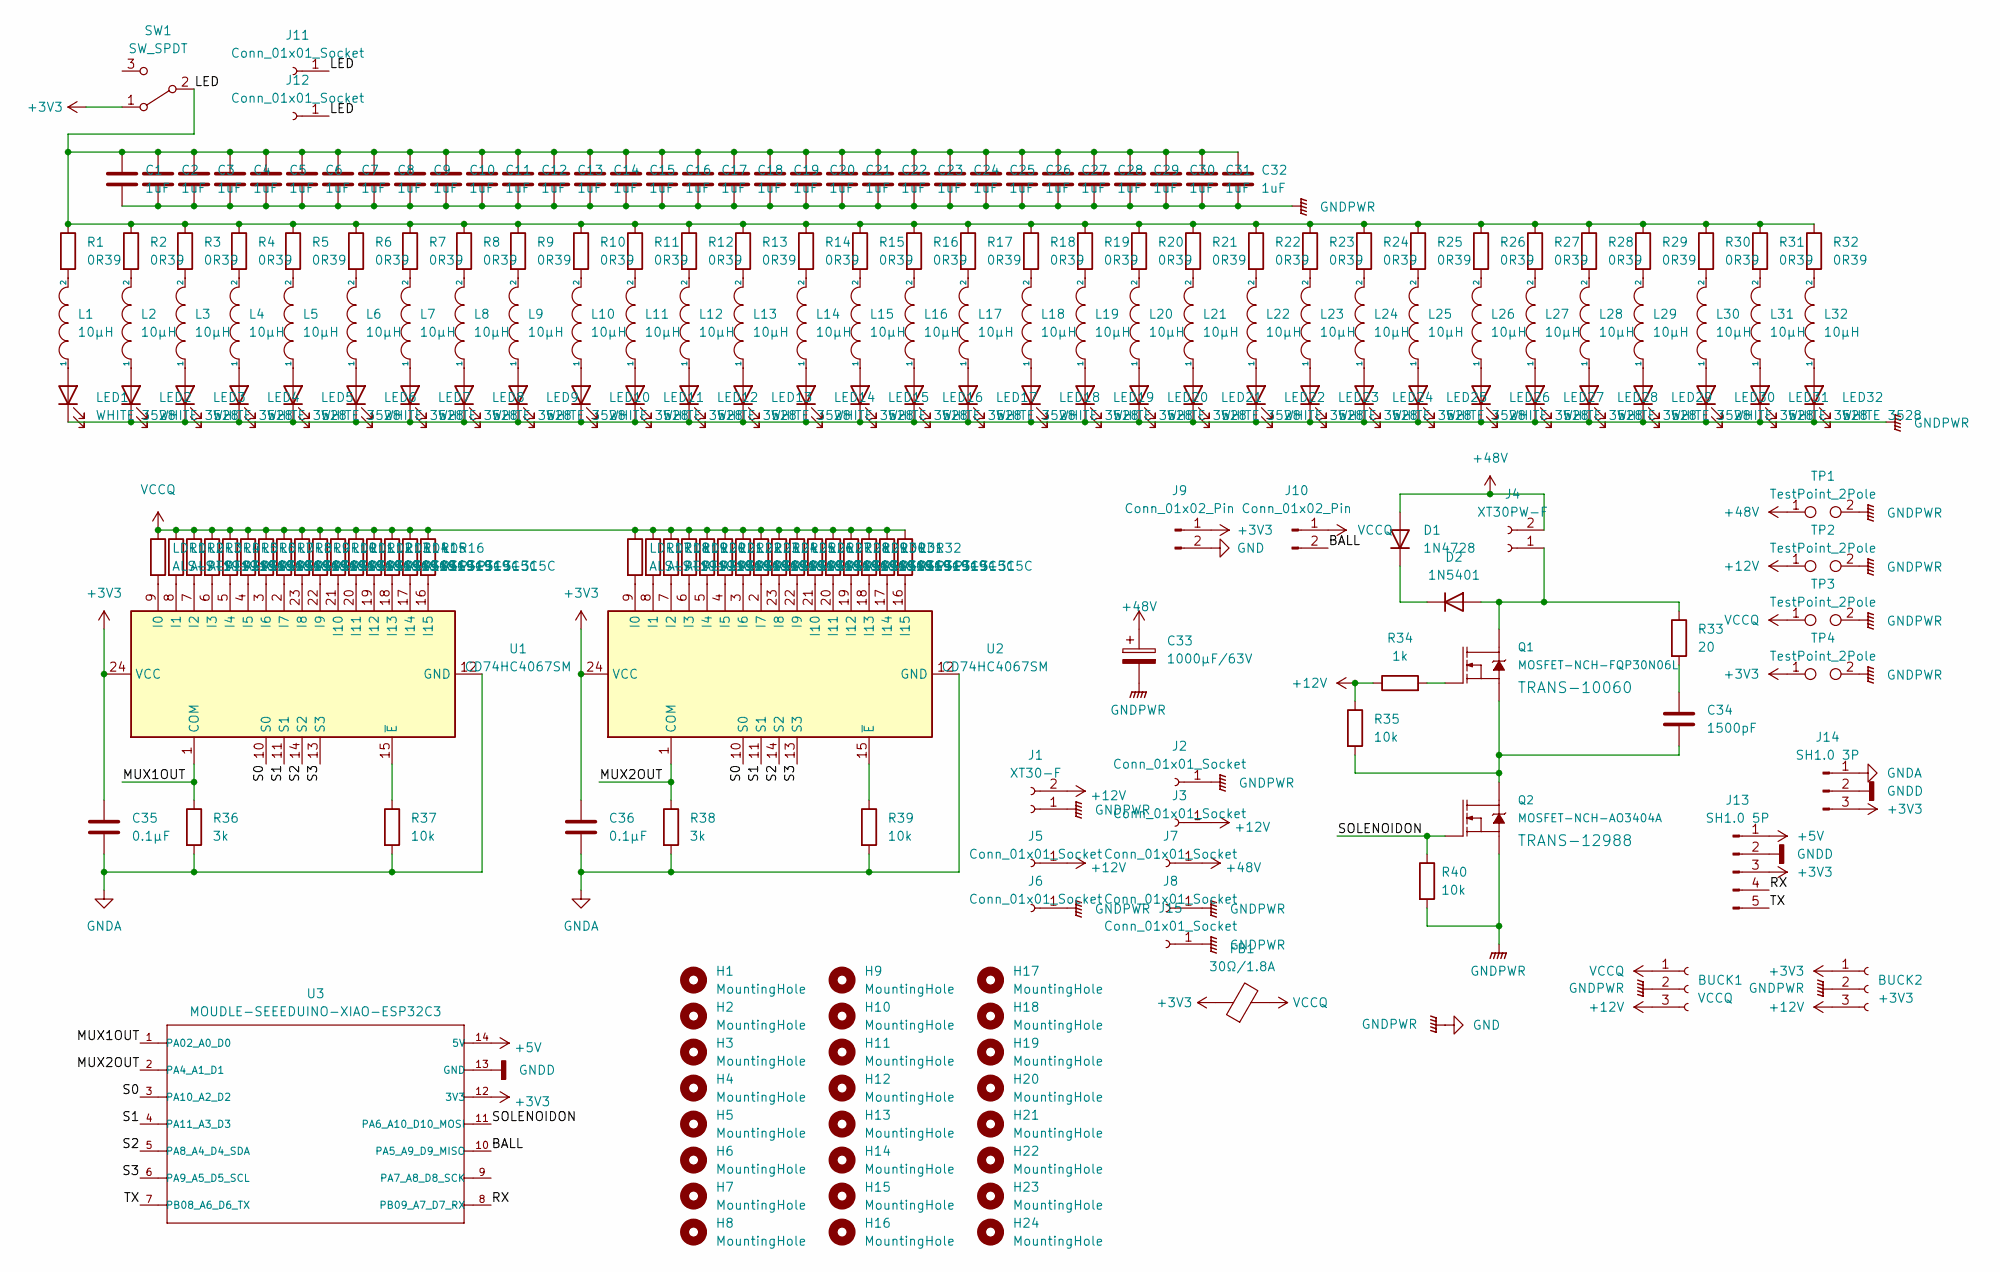
[picture p92: schematic layer1.kicad_sch]

Parts:
BUCK1: VCCQ; PinSocket_1x03_P2.54mm_Horizontal
BUCK2: +3V3; PinSocket_1x03_P2.54mm_Horizontal
C1, C2, C3, C4, C5, C6, C7, C8, C9, C10, C11, C12, C13, C14, C15, C16, C17, C18, C19, C20, C21, C22, C23, C24, C25, C26, C27, C28, C29, C30, C31, C32: 1uF; C_0603_1608Metric
C33: 1000µF/63V; CP_Radial_D16.0mm_P7.50mm
C34: 1500pF; C_0603_1608Metric
C35, C36: 0.1μF; C_0603_1608Metric
D1: 1N4728; D_DO-41_SOD81_P10.16mm_Horizontal
D2: 1N5401; D_DO-27_P15.24mm_Horizontal
FB1: 30Ω/1.8A; C_0603_1608Metric
H1, H2, H3, H4, H5, H6, H7, H8, H9, H10, H11, H12, H13, H14, H15, H16, H17, H18, H19, H20, H21, H22, H23, H24: MountingHole; MountingHole_3.2mm_M3_Pad
J1: XT30-F; AMASS_XT30UPB-F_1x02_P5.0mm_Vertical
J2, J11, J15: Conn_01x01_Socket; SolderWirePad_1x01_SMD_1x2mm
J3, J5, J6, J7, J8: Conn_01x01_Socket; SolderWirePad_1x01_SMD_5x10mm
J4: XT30PW-F; AMASS_XT30UPB-F_1x02_P5.0mm_Vertical
J9, J10: Conn_01x02_Pin; PinHeader_1x02_P2.54mm_Vertical
J12: Conn_01x01_Socket; SolderWire-0.5sqmm_1x01_D0.9mm_OD2.1mm
J13: SH1.0 5P; JST_SH_BM05B-SRSS-TB_1x05-1MP_P1.00mm_Vertical
J14: SH1.0 3P; JST_SH_BM03B-SRSS-TB_1x03-1MP_P1.00mm_Vertical
L1, L2, L3, L4, L5, L6, L7, L8, L9, L10, L11, L12, L13, L14, L15, L16, L17, L18, L19, L20, L21, L22, L23, L24, L25, L26, L27, L28, L29, L30, L31, L32: 10µH; L_0805_2012Metric
LDR1, LDR2, LDR3, LDR4, LDR5, LDR6, LDR7, LDR8, LDR9, LDR10, LDR11, LDR12, LDR13, LDR14, LDR15, LDR16, LDR17, LDR18, LDR19, LDR20, LDR21, LDR22, LDR23, LDR24, LDR25, LDR26, LDR27, LDR28, LDR29, LDR30, LDR31, LDR32: ALS-PT19-315C; D_0603_1608Metric
LED1, LED2, LED3, LED4, LED5, LED6, LED7, LED8, LED9, LED10, LED11, LED12, LED13, LED14, LED15, LED16, LED17, LED18, LED19, LED20, LED21, LED22, LED23, LED24, LED25, LED26, LED27, LED28, LED29, LED30, LED31, LED32: WHITE 3528; CP_EIA-3528-12_Kemet-T
Q1: MOSFET-NCH-FQP30N06L; TO-220-3_Vertical
Q2: MOSFET-NCH-AO3404A; TSOT-23
R1, R2, R3, R4, R5, R6, R7, R8, R9, R10, R11, R12, R13, R14, R15, R16, R17, R18, R19, R20, R21, R22, R23, R24, R25, R26, R27, R28, R29, R30, R31, R32: 0R39; R_0603_1608Metric
R33: 20; R_0603_1608Metric
R34: 1k; R_0603_1608Metric
R35, R37, R39, R40: 10k; R_0603_1608Metric
R36, R38: 3k; R_0603_1608Metric
SW1: SW_SPDT; SWITCH_SPDT_PTH_11.6X4.0MM
TP1, TP2, TP3, TP4: TestPoint_2Pole; TestPoint_2Pads_Pitch2.54mm_Drill0.8mm
U1, U2: CD74HC4067SM; SOIC-24W_7.5x15.4mm_P1.27mm
U3: MOUDLE-SEEEDUINO-XIAO-ESP32C3; xiao-esp32c3

Connections:
+3V3: BUCK2.1, C35.1, C36.1, FB1.1, J9.1, J13.3, J14.3, SW1.1 (A), TP4.1, U1.24 (VCC), U2.24 (VCC), U3.12 (3V3)
+5V: J13.1, U3.14 (5V)
+12V: BUCK1.3, BUCK2.3, J1.2, J3.1, J5.1, R34.1, R35.1, TP2.1
+48V: C33.1, D1.2 (A), J4.2, J7.1, TP1.1
BALL: J10.2, U3.10 (PA5_A9_D9_MISO)
GND: BUCK1.2, BUCK2.2, C1.2, C2.2, C3.2, C4.2, C5.2, C6.2, C7.2, C8.2, C9.2, C10.2, C11.2, C12.2, C13.2, C14.2, C15.2, C16.2, C17.2, C18.2, C19.2, C20.2, C21.2, C22.2, C23.2, C24.2, C25.2, C26.2, C27.2, C28.2, C29.2, C30.2, C31.2, C32.2, C33.2, J1.1, J2.1, J6.1, J8.1, J9.2, J15.1, LED1.1 (K), LED2.1 (K), LED3.1 (K), LED4.1 (K), LED5.1 (K), LED6.1 (K), LED7.1 (K), LED8.1 (K), LED9.1 (K), LED10.1 (K), LED11.1 (K), LED12.1 (K), LED13.1 (K), LED14.1 (K), LED15.1 (K), LED16.1 (K), LED17.1 (K), LED18.1 (K), LED19.1 (K), LED20.1 (K), LED21.1 (K), LED22.1 (K), LED23.1 (K), LED24.1 (K), LED25.1 (K), LED26.1 (K), LED27.1 (K), LED28.1 (K), LED29.1 (K), LED30.1 (K), LED31.1 (K), LED32.1 (K), Q2.2 (S), R40.2, TP1.2, TP2.2, TP3.2, TP4.2
GNDA: C35.2, C36.2, J14.1, R36.2, R37.2, R38.2, R39.2, U1.12 (GND), U2.12 (GND)
GNDD: J13.2, J14.2, U3.13 (GND)
LED: C1.1, C2.1, C3.1, C4.1, C5.1, C6.1, C7.1, C8.1, C9.1, C10.1, C11.1, C12.1, C13.1, C14.1, C15.1, C16.1, C17.1, C18.1, C19.1, C20.1, C21.1, C22.1, C23.1, C24.1, C25.1, C26.1, C27.1, C28.1, C29.1, C30.1, C31.1, C32.1, J11.1, J12.1, R1.1, R2.1, R3.1, R4.1, R5.1, R6.1, R7.1, R8.1, R9.1, R10.1, R11.1, R12.1, R13.1, R14.1, R15.1, R16.1, R17.1, R18.1, R19.1, R20.1, R21.1, R22.1, R23.1, R24.1, R25.1, R26.1, R27.1, R28.1, R29.1, R30.1, R31.1, R32.1, SW1.2 (B)
MUX1OUT: R36.1, U1.1 (COM), U3.1 (PA02_A0_D0)
MUX2OUT: R38.1, U2.1 (COM), U3.2 (PA4_A1_D1)
unnamed: C34.1, R33.2
unnamed: C34.2, Q1.3 (S), Q2.3 (D), R35.2
unnamed: D1.1 (K), D2.1 (K)
unnamed: D2.2 (A), J4.1, Q1.2 (D), R33.1
unnamed: L1.1, LED1.2 (A)
unnamed: L1.2, R1.2
unnamed: L2.1, LED2.2 (A)
unnamed: L2.2, R2.2
unnamed: L3.1, LED3.2 (A)
unnamed: L3.2, R3.2
unnamed: L4.1, LED4.2 (A)
unnamed: L4.2, R4.2
unnamed: L5.1, LED5.2 (A)
unnamed: L5.2, R5.2
unnamed: L6.1, LED6.2 (A)
unnamed: L6.2, R6.2
unnamed: L7.1, LED7.2 (A)
unnamed: L7.2, R7.2
unnamed: L8.1, LED8.2 (A)
unnamed: L8.2, R8.2
unnamed: L9.1, LED9.2 (A)
unnamed: L9.2, R9.2
unnamed: L10.1, LED10.2 (A)
unnamed: L10.2, R10.2
unnamed: L11.1, LED11.2 (A)
unnamed: L11.2, R11.2
unnamed: L12.1, LED12.2 (A)
unnamed: L12.2, R12.2
unnamed: L13.1, LED13.2 (A)
unnamed: L13.2, R13.2
unnamed: L14.1, LED14.2 (A)
unnamed: L14.2, R14.2
unnamed: L15.1, LED15.2 (A)
unnamed: L15.2, R15.2
unnamed: L16.1, LED16.2 (A)
unnamed: L16.2, R16.2
unnamed: L17.1, LED17.2 (A)
unnamed: L17.2, R17.2
unnamed: L18.1, LED18.2 (A)
unnamed: L18.2, R18.2
unnamed: L19.1, LED19.2 (A)
unnamed: L19.2, R19.2
unnamed: L20.1, LED20.2 (A)
unnamed: L20.2, R20.2
unnamed: L21.1, LED21.2 (A)
unnamed: L21.2, R21.2
unnamed: L22.1, LED22.2 (A)
unnamed: L22.2, R22.2
unnamed: L23.1, LED23.2 (A)
unnamed: L23.2, R23.2
unnamed: L24.1, LED24.2 (A)
unnamed: L24.2, R24.2
unnamed: L25.1, LED25.2 (A)
unnamed: L25.2, R25.2
unnamed: L26.1, LED26.2 (A)
unnamed: L26.2, R26.2
unnamed: L27.1, LED27.2 (A)
unnamed: L27.2, R27.2
unnamed: L28.1, LED28.2 (A)
unnamed: L28.2, R28.2
unnamed: L29.1, LED29.2 (A)
unnamed: L29.2, R29.2
unnamed: L30.1, LED30.2 (A)
unnamed: L30.2, R30.2
unnamed: L31.1, LED31.2 (A)
unnamed: L31.2, R31.2
unnamed: L32.1, LED32.2 (A)
unnamed: L32.2, R32.2
unnamed: LDR1.2, U1.9 (I0)
unnamed: LDR2.2, U1.8 (I1)
unnamed: LDR3.2, U1.7 (I2)
unnamed: LDR4.2, U1.6 (I3)
unnamed: LDR5.2, U1.5 (I4)
unnamed: LDR6.2, U1.4 (I5)
unnamed: LDR7.2, U1.3 (I6)
unnamed: LDR8.2, U1.2 (I7)
unnamed: LDR9.2, U1.23 (I8)
unnamed: LDR10.2, U1.22 (I9)
unnamed: LDR11.2, U1.21 (I10)
unnamed: LDR12.2, U1.20 (I11)
unnamed: LDR13.2, U1.19 (I12)
unnamed: LDR14.2, U1.18 (I13)
unnamed: LDR15.2, U1.17 (I14)
unnamed: LDR16.2, U1.16 (I15)
unnamed: LDR17.2, U2.9 (I0)
unnamed: LDR18.2, U2.8 (I1)
unnamed: LDR19.2, U2.7 (I2)
unnamed: LDR20.2, U2.6 (I3)
unnamed: LDR21.2, U2.5 (I4)
unnamed: LDR22.2, U2.4 (I5)
unnamed: LDR23.2, U2.3 (I6)
unnamed: LDR24.2, U2.2 (I7)
unnamed: LDR25.2, U2.23 (I8)
unnamed: LDR26.2, U2.22 (I9)
unnamed: LDR27.2, U2.21 (I10)
unnamed: LDR28.2, U2.20 (I11)
unnamed: LDR29.2, U2.19 (I12)
unnamed: LDR30.2, U2.18 (I13)
unnamed: LDR31.2, U2.17 (I14)
unnamed: LDR32.2, U2.16 (I15)
unnamed: Q1.1 (G), R34.2
unnamed: R37.1, U1.15 (~E)
unnamed: R39.1, U2.15 (~E)
RX: J13.4, U3.8 (PB09_A7_D7_RX)
S0: U1.10 (S0), U2.10 (S0), U3.3 (PA10_A2_D2)
S1: U1.11 (S1), U2.11 (S1), U3.4 (PA11_A3_D3)
S2: U1.14 (S2), U2.14 (S2), U3.5 (PA8_A4_D4_SDA)
S3: U1.13 (S3), U2.13 (S3), U3.6 (PA9_A5_D5_SCL)
SOLENOIDON: Q2.1 (G), R40.1, U3.11 (PA6_A10_D10_MOSI)
TX: J13.5, U3.7 (PB08_A6_D6_TX)
VCCQ: BUCK1.1, FB1.2, J10.1, LDR1.1, LDR2.1, LDR3.1, LDR4.1, LDR5.1, LDR6.1, LDR7.1, LDR8.1, LDR9.1, LDR10.1, LDR11.1, LDR12.1, LDR13.1, LDR14.1, LDR15.1, LDR16.1, LDR17.1, LDR18.1, LDR19.1, LDR20.1, LDR21.1, LDR22.1, LDR23.1, LDR24.1, LDR25.1, LDR26.1, LDR27.1, LDR28.1, LDR29.1, LDR30.1, LDR31.1, LDR32.1, TP3.1
