8076ducc/robocup-2024/open/software design/microcontrollers/src/teensy2/main.cpp

#include "main.h"

PacketSerial Cam1Serial;
PacketSerial Cam2Serial;
PacketSerial BtSerial;
PacketSerial TeensySerial;

BtTxDataUnion bt_tx_data;
BtRxDataUnion bt_rx_data;
CamTxDataUnion cam_tx_data;
CamRxDataUnion cam_rx_data;
Teensy1TxDataUnion teensy_1_tx_data;
Teensy1RxDataUnion teensy_1_rx_data;

Robot robot;
Ball ball;
Goal yellow_goal;
Goal blue_goal;
Threads::Mutex lidar_data_lock;

void lidarThread()
{
  while (true)
  {
    robot.processLidar();
  }
}

void setup()
{
  robot.setUpSerial();
  robot.setUpLidar();
  threads.addThread(lidarThread);
}

void loop()
{
  robot.updateSerial();
  robot.sendSerial();

  teensy_1_rx_data.data.yellow_goal.current_pose = yellow_goal.current_pose;
  teensy_1_rx_data.data.blue_goal.current_pose = blue_goal.current_pose;
  cam_rx_data.data.track_orange = true;

  if (!digitalRead(DIP_1))
  {
    teensy_1_rx_data.data.dip_1_on = true;
  }
  else
  {
    teensy_1_rx_data.data.dip_1_on = false;
  }

  if (!digitalRead(DIP_2))
  {
    teensy_1_rx_data.data.dip_2_on = true;
  }
  else
  {
    teensy_1_rx_data.data.dip_2_on = false;
  }

  if (!digitalRead(DIP_3))
  {
    teensy_1_rx_data.data.dip_3_on = true;
  }
  else
  {
    teensy_1_rx_data.data.dip_3_on = false;
  }

  if (!digitalRead(DIP_4))
  {
    teensy_1_rx_data.data.dip_4_on = true;
    cam_rx_data.data.track_yellow = true;
    cam_rx_data.data.track_blue = false;
  }
  else
  {
    teensy_1_rx_data.data.dip_4_on = false;
    cam_rx_data.data.track_yellow = false;
    cam_rx_data.data.track_blue = true;
  }

  cam_rx_data.data.track_blue = true;
  cam_rx_data.data.track_yellow = false;

  robot.getRobotPose();
}
