8076ducc/robocup-2024/open/software design/microcontrollers/src/imu/main.h

#pragma once

#ifndef MAIN_H
#define MAIN_H

// #define DEBUG
// #define SERIAL_DEBUG

#include <common.h>
#include <Adafruit_BNO08x.h>
// #include <ArduinoEigen.h>
#include <ArduinoEigenDense.h>

#endif
