8076ducc/robocup-2024/open/software design/microcontrollers/include/common.h

#pragma once

#ifndef COMMON_H
#define COMMON_H

#include <Arduino.h>
#include <iterator>
#include <vector>
#include <math.h>
#include <digitalWriteFast.h>
#include <PacketSerial.h>

// shared project header files
#include <serial.h>
#include <utils.h>
#include <functions.h>

#endif
