8076ducc/robocup-2024/open/software design/microcontrollers/src/teensy1/line.cpp

#include "main.h"

double mean(std::vector<double> v)
{
    double sum = 0.0;
    for (int i = 0; i < v.size(); i++)
    {
        sum += v[i];
    }
    return sum / v.size();
}

void Line::horizontalLinearRegression()
{
    double x_mean = mean(x);
    double y_mean = mean(y);
    double numerator = 0.0;
    double denominator = 0.0;
    for (int i = 0; i < x.size(); i++)
    {
        numerator += (x[i] - x_mean) * (y[i] - y_mean);
        denominator += pow(x[i] - x_mean, 2);
    }
    slope = numerator / denominator;
    intercept = y_mean - slope * x_mean;

    //   Serial.print("y = ");
    //   Serial.print(slope);
    //   Serial.print("x + ");
    //   Serial.println(intercept);
}

void Line::verticalLinearRegression()
{
    double x_mean = mean(x);
    double y_mean = mean(y);
    double numerator = 0.0;
    double denominator = 0.0;
    for (int i = 0; i < x.size(); i++)
    {
        numerator += (y[i] - y_mean) * (x[i] - x_mean);
        denominator += pow(y[i] - y_mean, 2);
    }
    slope = numerator / denominator;
    intercept = x_mean - slope * y_mean;

    //   Serial.print("x = ");
    //   Serial.print(slope);
    //   Serial.print("y + ");
    //   Serial.println(intercept);
}
